paenian/Delta-Conveyor-Belt/kossel - 240mm triangle/ancillary STLs/HVplate.stl

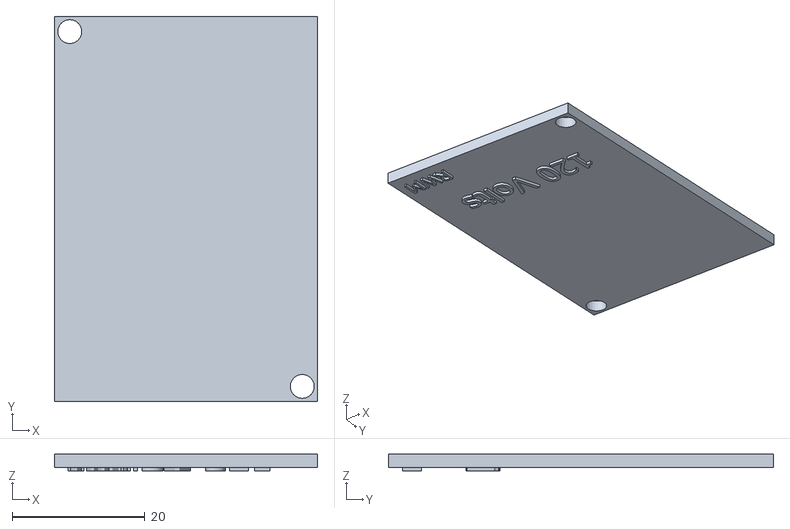
[picture p16: CAD file, 2020-08-09]
kossel - 240mm triangle/ancillary STLs/HVplate.stl
39.6 x 58.1 x 2.50
