paenian/Delta-Conveyor-Belt/kossel - 240mm triangle/motor_drive_gear.stl

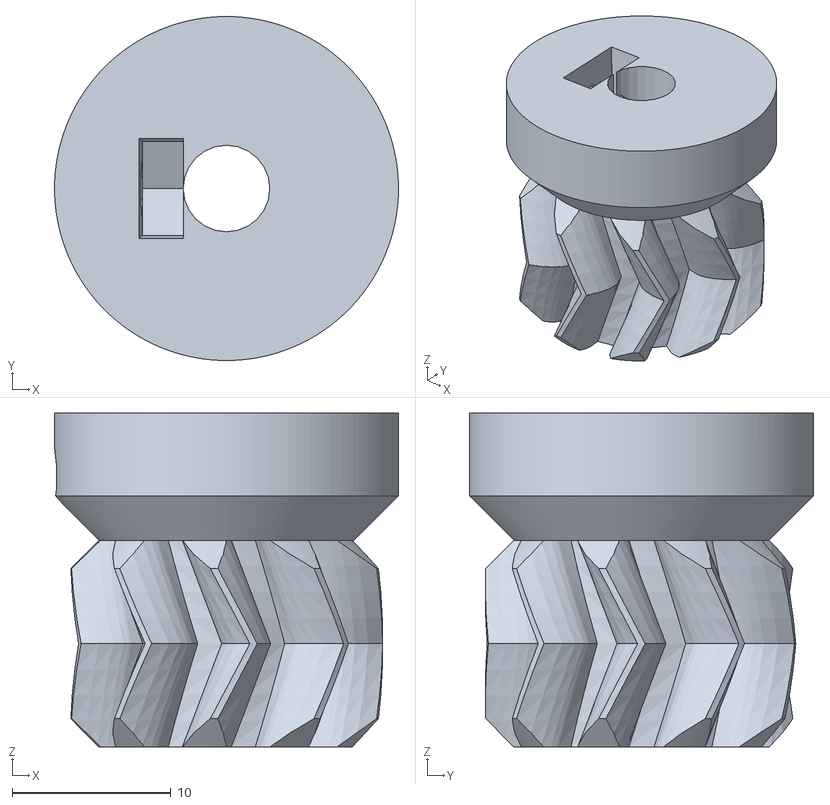
[picture p17: CAD file, 2020-04-07]
kossel - 240mm triangle/motor_drive_gear.stl
21.6 x 21.6 x 21.0
