paenian/Delta-Conveyor-Belt/kossel linear plus/triangles.dxf

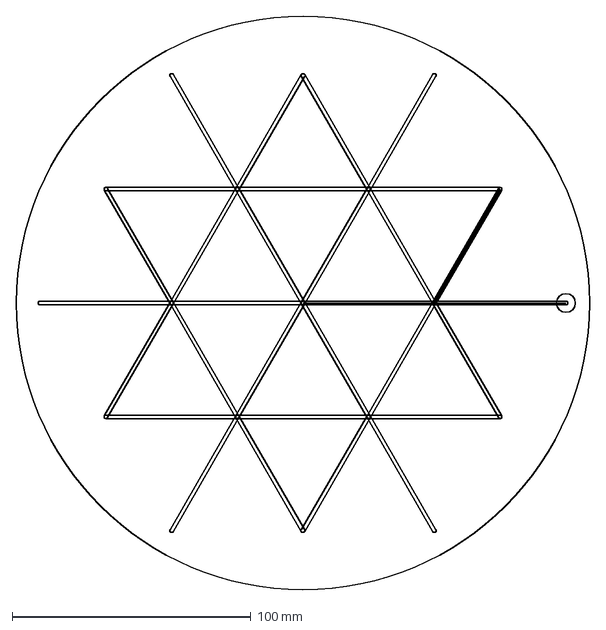
[picture p18: CAD file, 2020-09-24]
kossel linear plus/triangles.dxf
240.0 x 240.0 mm
