paenian/Delta-Conveyor-Belt/prusa mini/bed lasercutting/rounded_notch-425x155.dxf

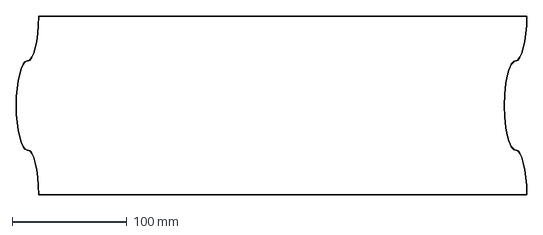
[picture p19: CAD file, 2021-02-12]
prusa mini/bed lasercutting/rounded_notch-425x155.dxf
444.4 x 155.0 mm
