paenian/Delta-Conveyor-Belt/prusa mini/ejector 2.0/rear motor clamp.stl

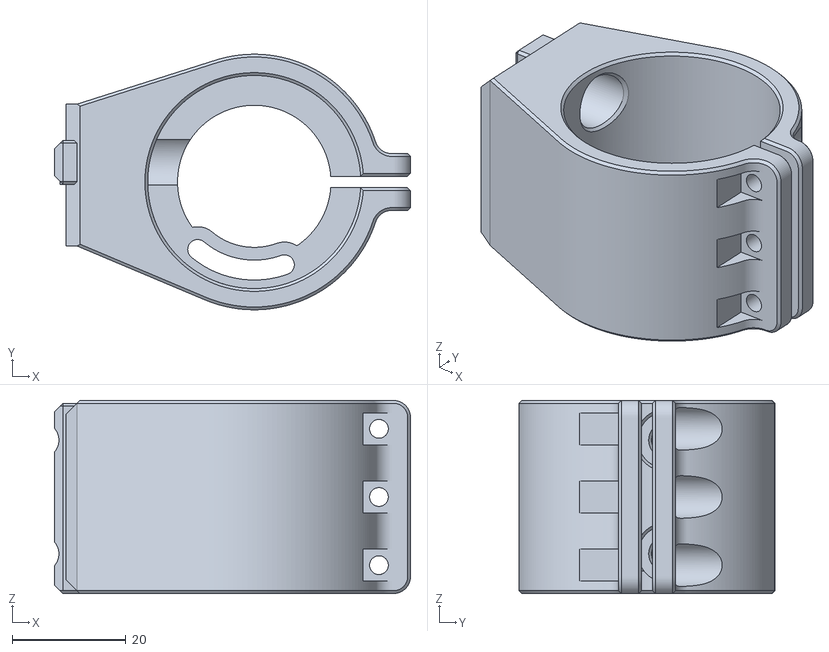
[picture p20: CAD file, 2021-02-12]
prusa mini/ejector 2.0/rear motor clamp.stl
62.7 x 45.0 x 34.0
