paenian/Delta-Conveyor-Belt/prusa mini/ejector 3.0/failed coupler iterations/rear motor plate.stl

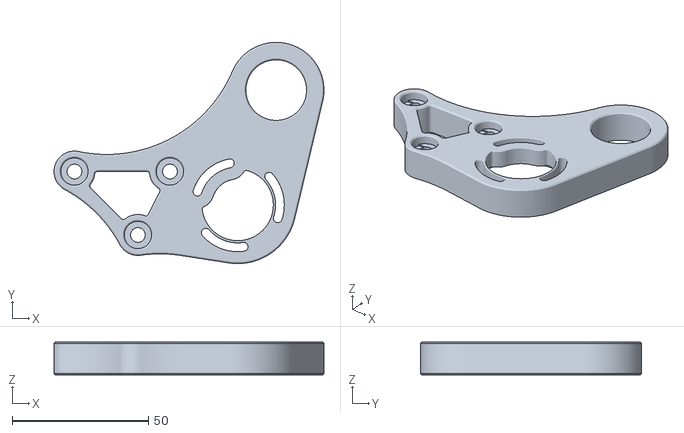
[picture p21: CAD file, 2021-04-25]
prusa mini/ejector 3.0/failed coupler iterations/rear motor plate.stl
98.9 x 81.1 x 12.0
