paenian/Delta-Conveyor-Belt/prusa mini/ejector 3.0/pi_3_case_bottom.stl

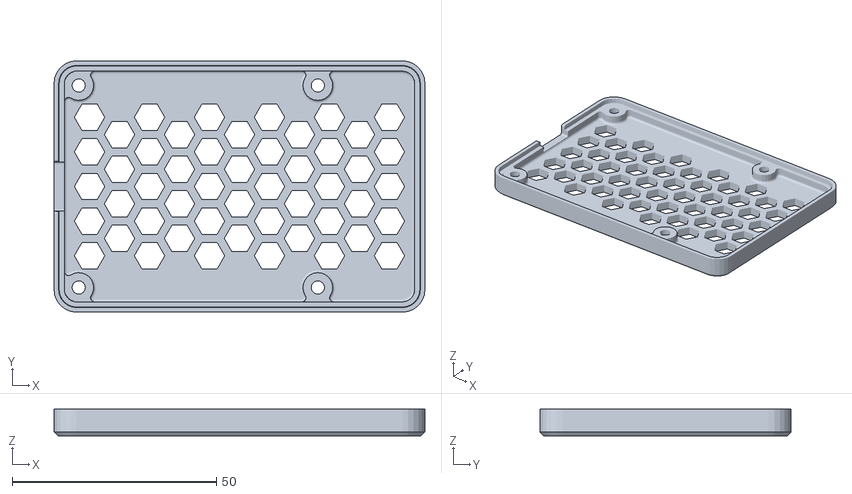
[picture p22: CAD file, 2021-04-25]
prusa mini/ejector 3.0/pi_3_case_bottom.stl
90.9 x 61.6 x 6.57
