paenian/Delta-Conveyor-Belt/prusa mini/experimental parts/motor_gear.stl

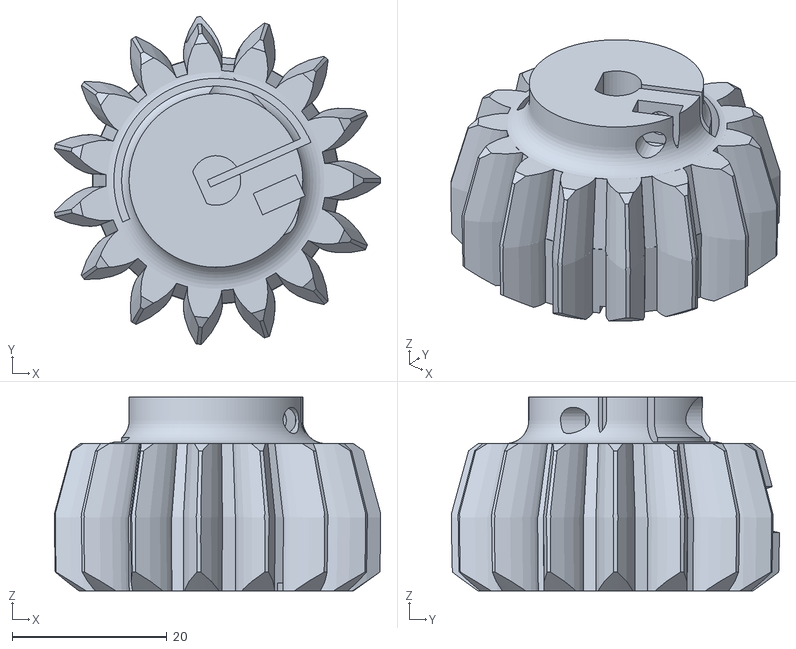
[picture p23: CAD file, 2021-02-12]
prusa mini/experimental parts/motor_gear.stl
42.1 x 42.3 x 25.0
