paenian/Delta-Conveyor-Belt/prusa mini/front spool holder.stl

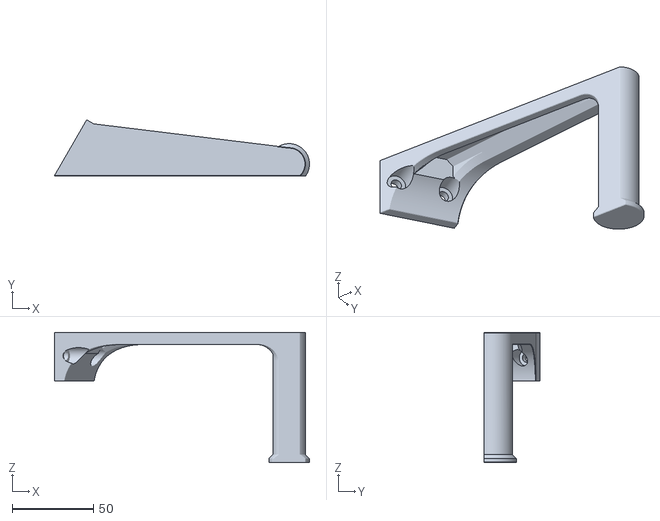
[picture p24: CAD file, 2020-11-18]
prusa mini/front spool holder.stl
156.6 x 34.6 x 80.0
