paenian/Delta-Conveyor-Belt/prusa mini/raspi/pi camera mount.stl

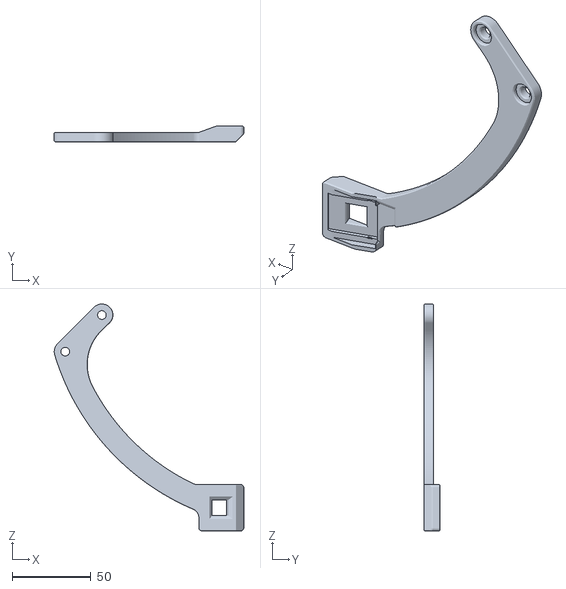
[picture p25: CAD file, 2020-11-18]
prusa mini/raspi/pi camera mount.stl
120.2 x 10.0 x 144.0
