paenian/Delta-Conveyor-Belt/tft35right.stl

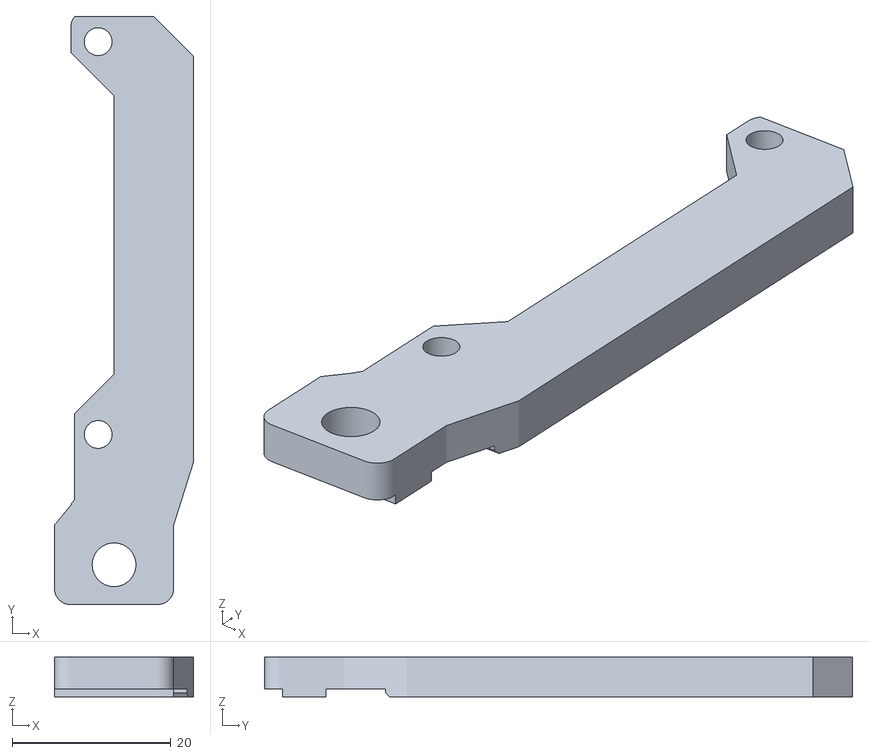
[picture p26: CAD file, 2020-08-09]
tft35right.stl
17.5 x 74.0 x 5.00
