paenian/Delta-Conveyor-Belt/kossel - 240mm triangle/ancillary STLs/pwr_shield4.stl

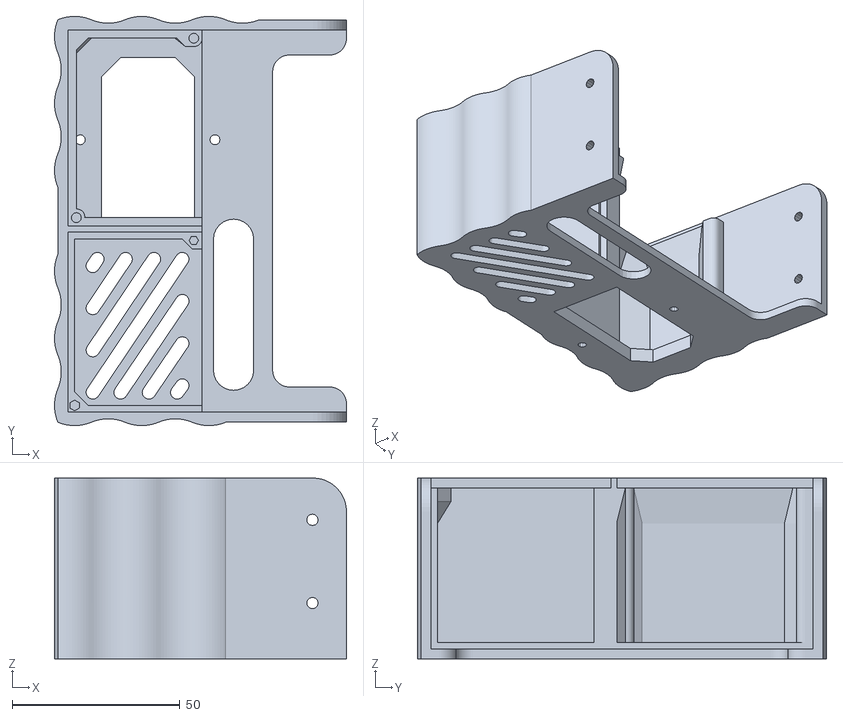
[picture p27: CAD file, 2020-08-09]
kossel - 240mm triangle/ancillary STLs/pwr_shield4.stl
87.0 x 121.9 x 53.9
