paenian/Delta-Conveyor-Belt/kossel - 240mm triangle/fan mount.stl

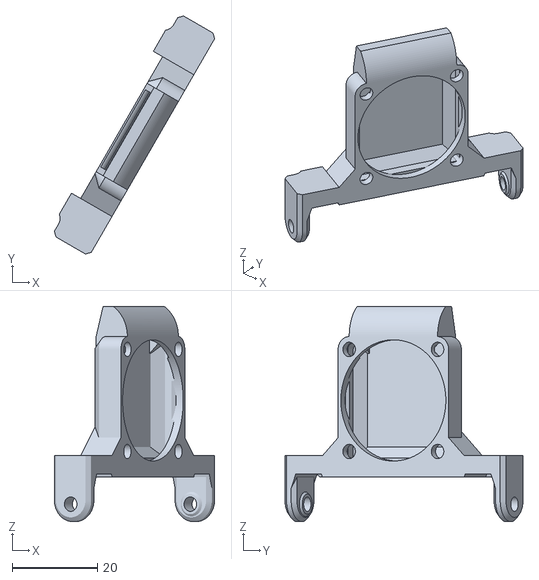
[picture p28: CAD file, 2020-04-07]
kossel - 240mm triangle/fan mount.stl
37.7 x 56.0 x 50.6
