paenian/Delta-Conveyor-Belt/kossel linear plus/o-ring groove.dxf

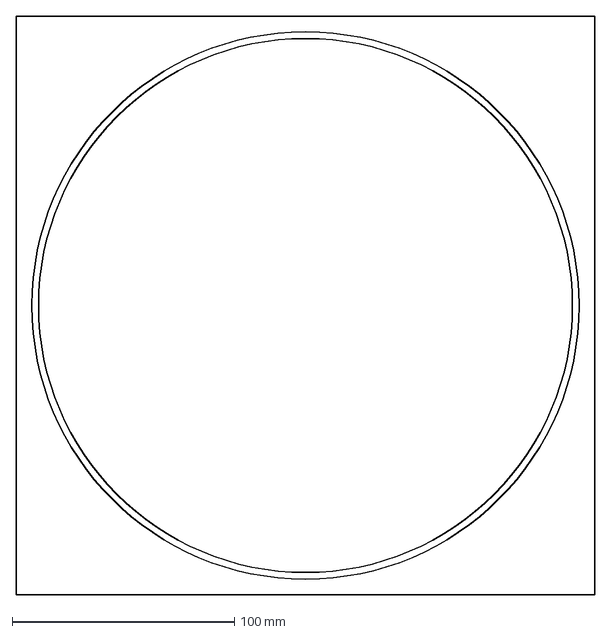
[picture p29: CAD file, 2020-09-24]
kossel linear plus/o-ring groove.dxf
260.0 x 260.0 mm
