paenian/Delta-Conveyor-Belt/prusa mini/bed lasercutting/chevron-425x155.dxf

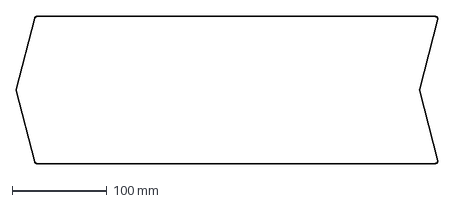
[picture p30: CAD file, 2021-02-12]
prusa mini/bed lasercutting/chevron-425x155.dxf
444.3 x 155.0 mm
