paenian/Delta-Conveyor-Belt/prusa mini/ejector 2.0/tensioner body.stl

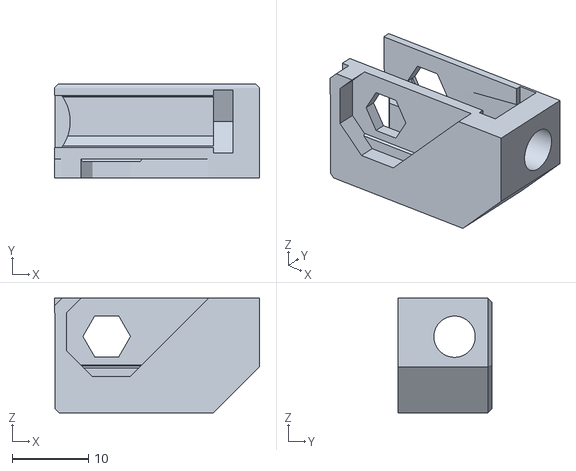
[picture p31: CAD file, 2021-02-12]
prusa mini/ejector 2.0/tensioner body.stl
26.8 x 12.3 x 15.0
