paenian/Delta-Conveyor-Belt/prusa mini/ejector 3.0/failed coupler iterations/Body37.stl

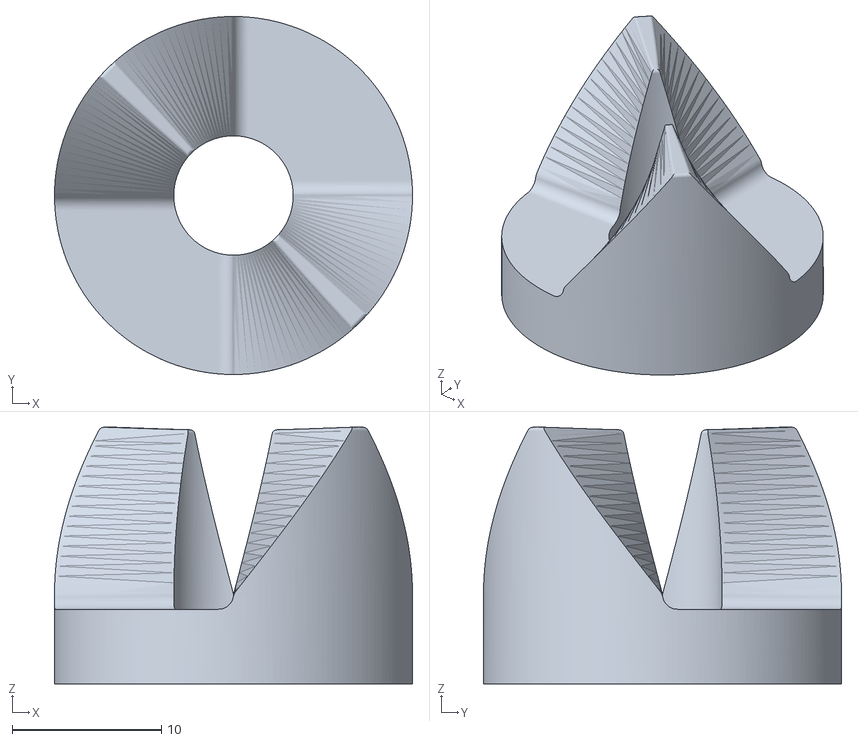
[picture p32: CAD file, 2021-02-26]
prusa mini/ejector 3.0/failed coupler iterations/Body37.stl
24.0 x 24.0 x 17.2
