paenian/Delta-Conveyor-Belt/prusa mini/ejector 3.0/pi_3_case_top.stl

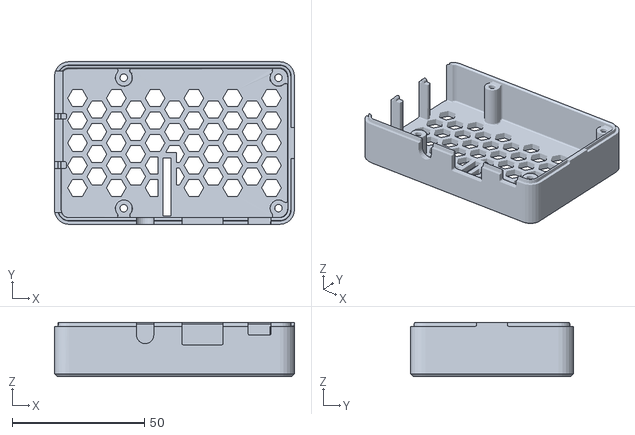
[picture p33: CAD file, 2021-04-25]
prusa mini/ejector 3.0/pi_3_case_top.stl
90.9 x 61.6 x 20.5
