paenian/Delta-Conveyor-Belt/prusa mini/experimental parts/belt_gear.stl

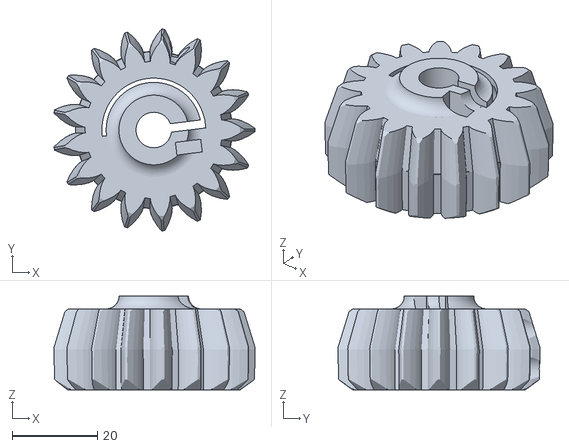
[picture p34: CAD file, 2021-02-12]
prusa mini/experimental parts/belt_gear.stl
47.2 x 47.4 x 22.0
