paenian/Delta-Conveyor-Belt/prusa mini/motor_gear.stl

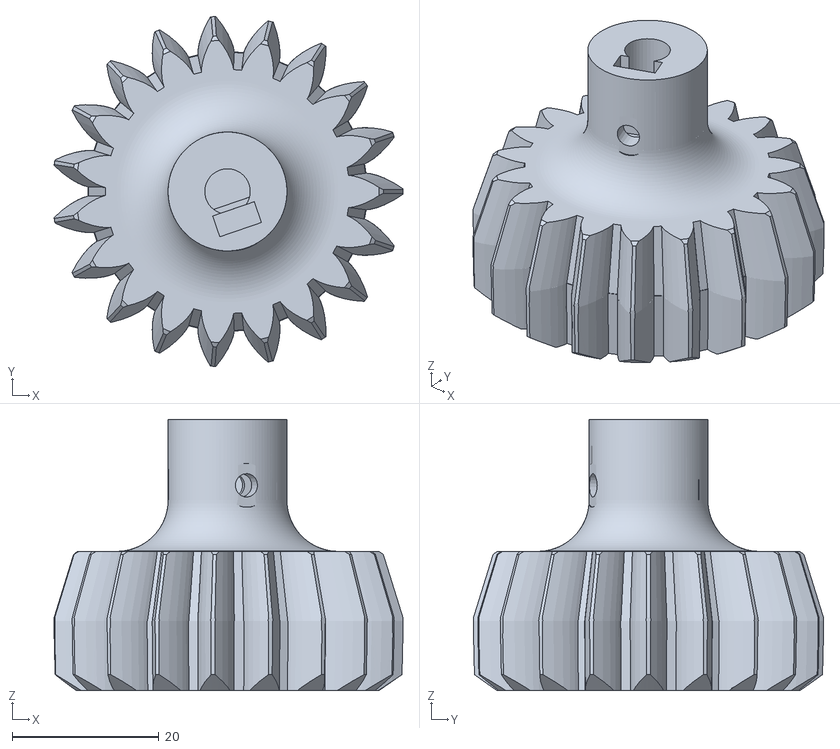
[picture p35: CAD file, 2020-11-18]
prusa mini/motor_gear.stl
47.6 x 47.7 x 37.0
