paenian/Delta-Conveyor-Belt/prusa mini/raspi/raspi_case_top.stl

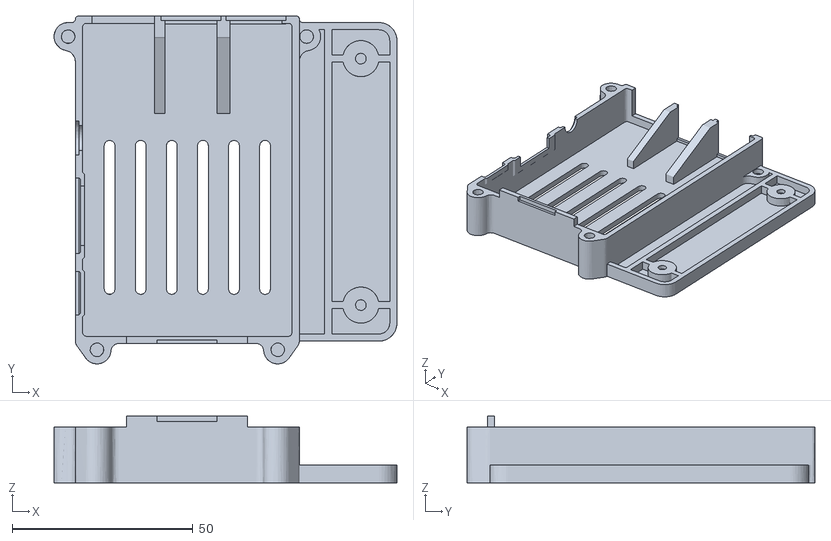
[picture p36: CAD file, 2020-08-16]
prusa mini/raspi/raspi_case_top.stl
94.9 x 96.2 x 18.5
