paenian/Delta-Conveyor-Belt/tft35left.stl

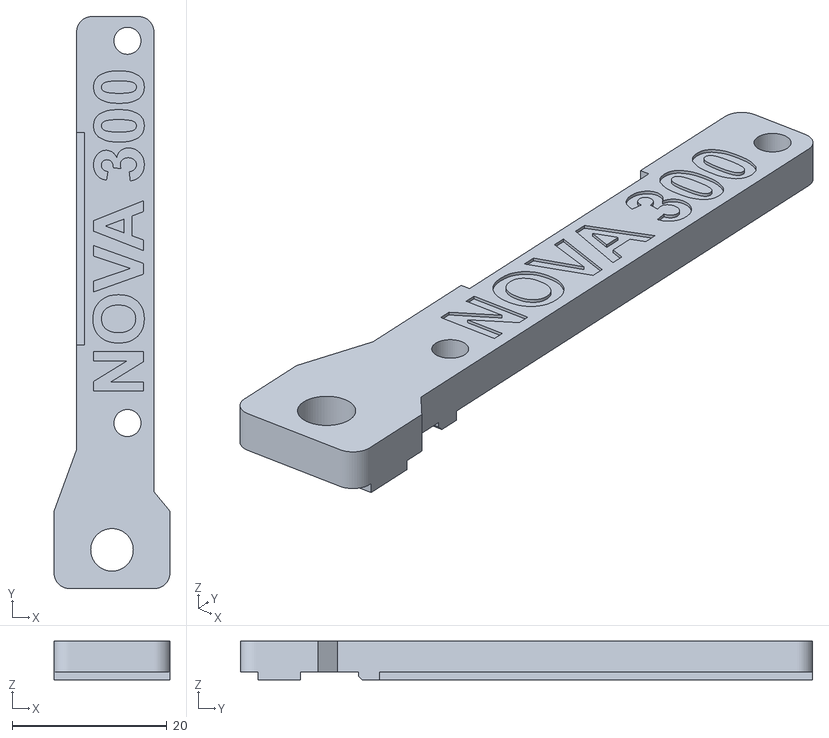
[picture p37: CAD file, 2020-08-09]
tft35left.stl
15.0 x 74.0 x 5.00
