paenian/Delta-Conveyor-Belt/kossel - 240mm triangle/ancillary STLs/LVplate.stl

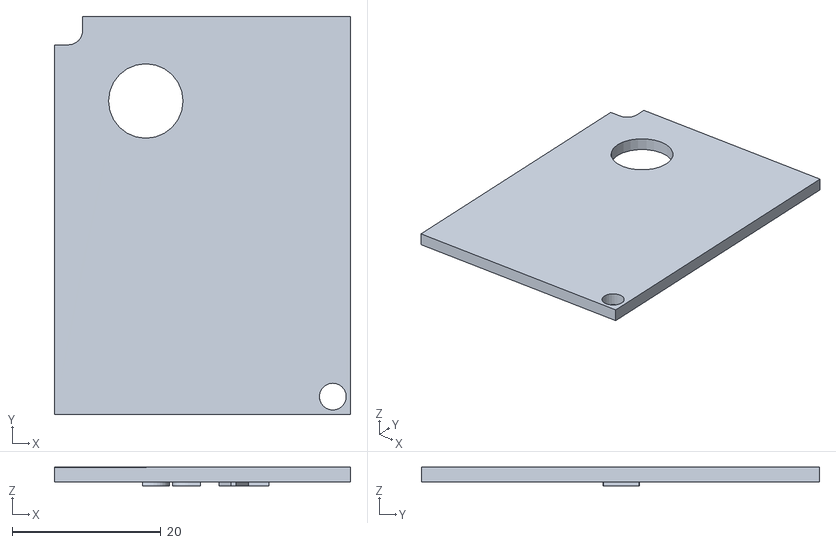
[picture p38: CAD file, 2020-08-09]
kossel - 240mm triangle/ancillary STLs/LVplate.stl
39.8 x 53.5 x 2.51
