paenian/Delta-Conveyor-Belt/kossel linear plus/vacuum hole.dxf

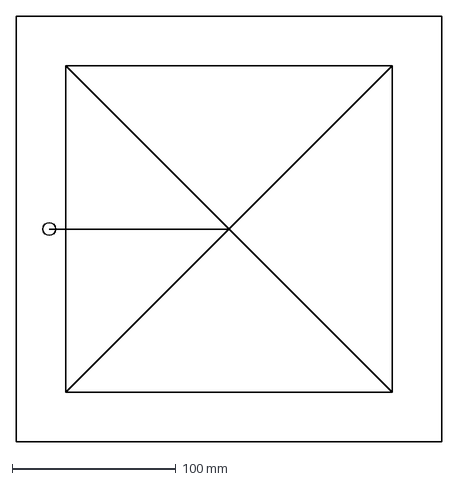
[picture p39: CAD file, 2020-09-24]
kossel linear plus/vacuum hole.dxf
260.0 x 260.0 mm
