paenian/Delta-Conveyor-Belt/prusa mini/belt_425mm.dxf

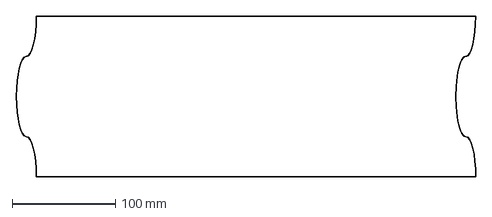
[picture p40: CAD file, 2020-11-02]
prusa mini/belt_425mm.dxf
444.4 x 155.0 mm
