paenian/Delta-Conveyor-Belt/prusa mini/ejector 2.0/lifted belt shaft mount - fixed bushing.stl

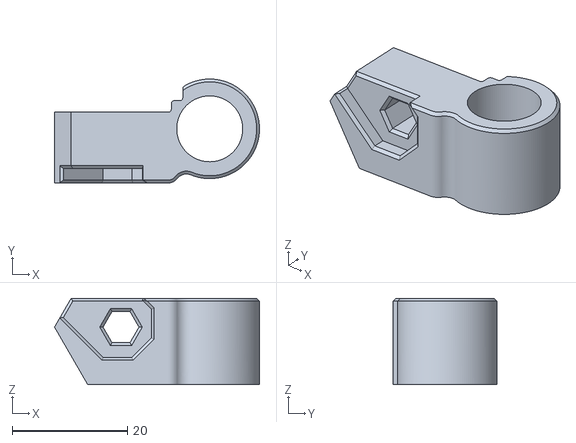
[picture p41: CAD file, 2021-02-12]
prusa mini/ejector 2.0/lifted belt shaft mount - fixed bushing.stl
35.6 x 18.0 x 15.0
