paenian/Delta-Conveyor-Belt/prusa mini/ejector 3.0/failed coupler iterations/split_spider.stl

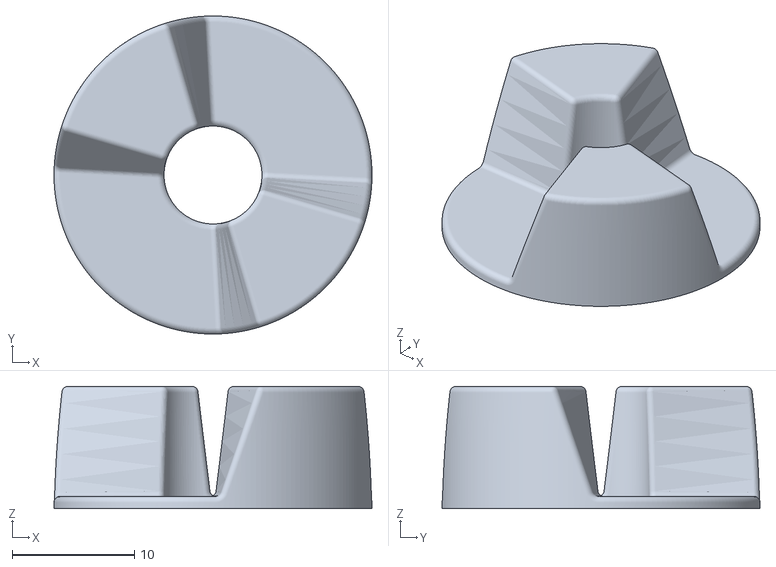
[picture p42: CAD file, 2021-02-26]
prusa mini/ejector 3.0/failed coupler iterations/split_spider.stl
26.0 x 26.0 x 10.0
