paenian/Delta-Conveyor-Belt/prusa mini/ejector 3.0/rear motor plate.stl

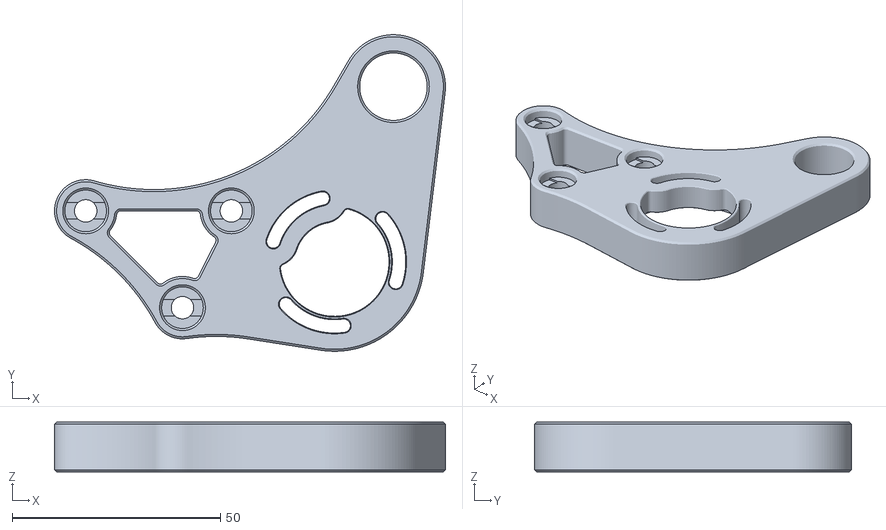
[picture p43: CAD file, 2021-03-26]
prusa mini/ejector 3.0/rear motor plate.stl
93.9 x 76.1 x 12.0
