paenian/Delta-Conveyor-Belt/prusa mini/experimental parts/foot.stl

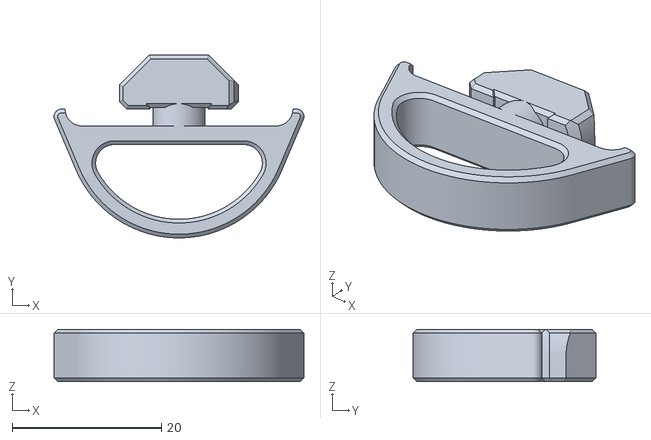
[picture p44: CAD file, 2021-02-12]
prusa mini/experimental parts/foot.stl
33.5 x 24.5 x 7.00
