paenian/Delta-Conveyor-Belt/prusa mini/raspi/raspi_case_bottom.stl

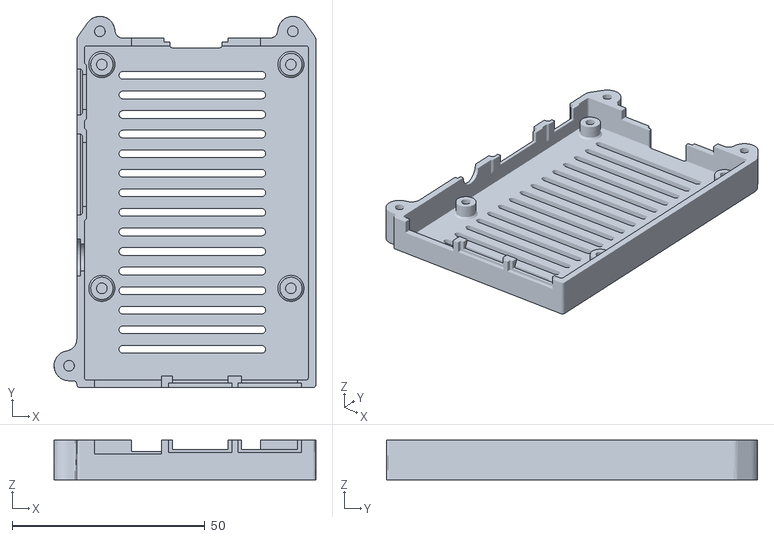
[picture p45: CAD file, 2020-08-16]
prusa mini/raspi/raspi_case_bottom.stl
67.9 x 96.2 x 10.3
