paenian/Delta-Conveyor-Belt/tft24left.stl

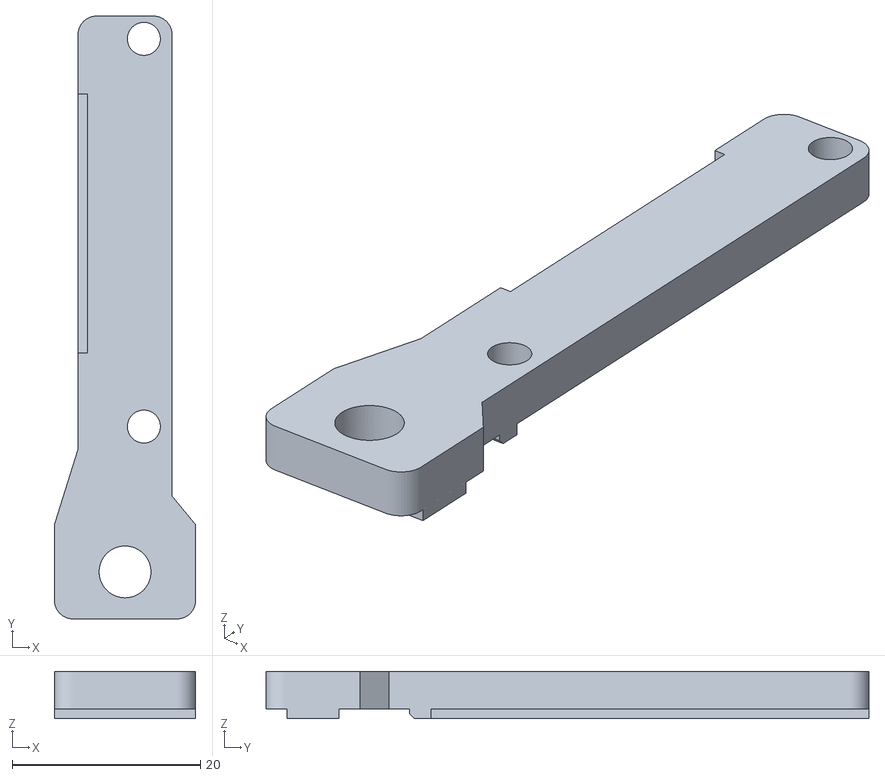
[picture p46: CAD file, 2020-08-09]
tft24left.stl
15.0 x 64.0 x 5.00
