paenian/Delta-Conveyor-Belt/kossel - 240mm triangle/ancillary STLs/Raspberry_Pi_3_Case_-_Bottom.stl

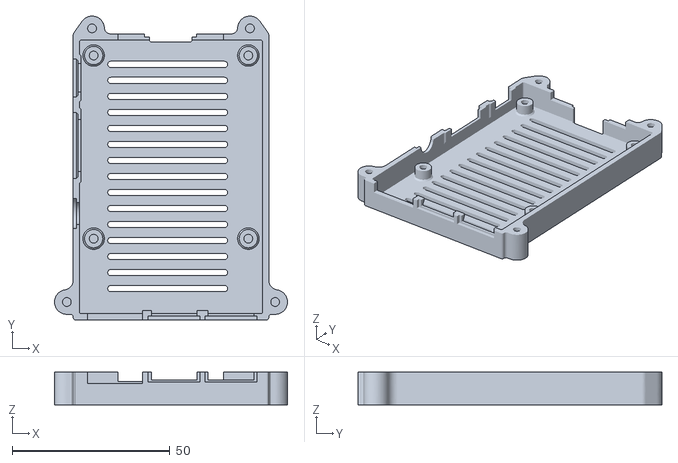
[picture p47: CAD file, 2020-08-09]
kossel - 240mm triangle/ancillary STLs/Raspberry_Pi_3_Case_-_Bottom.stl
73.8 x 96.2 x 10.3
