paenian/Delta-Conveyor-Belt/kossel - 240mm triangle/tensioner arm(Mirror).stl

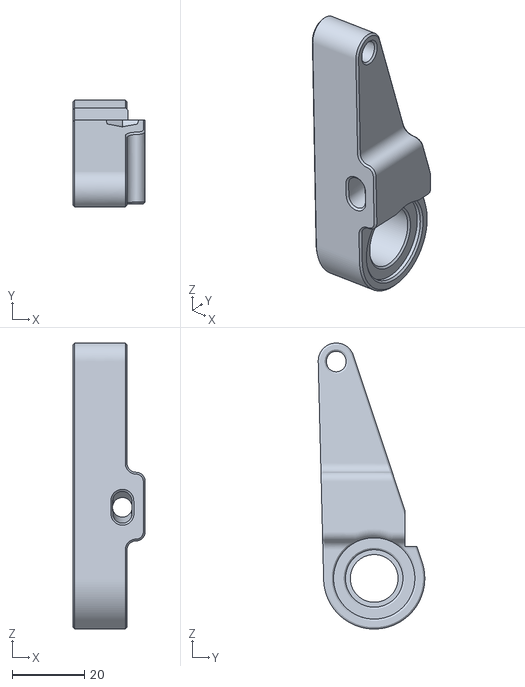
[picture p48: CAD file, 2020-04-07]
kossel - 240mm triangle/tensioner arm(Mirror).stl
20.0 x 29.5 x 79.1
