paenian/Delta-Conveyor-Belt/prusa mini/ejector 2.0/rear motor plate.stl

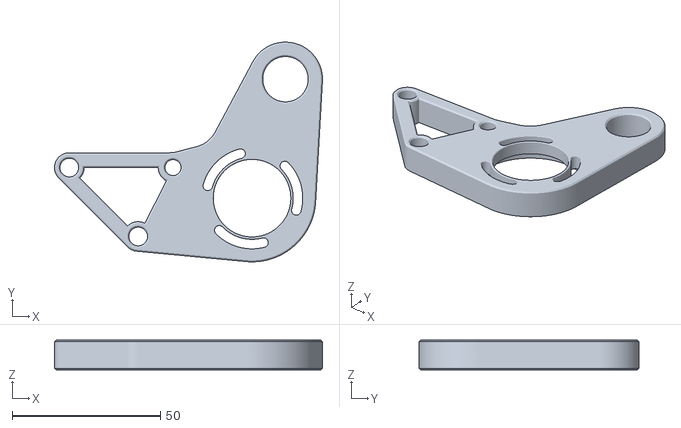
[picture p49: CAD file, 2021-02-12]
prusa mini/ejector 2.0/rear motor plate.stl
90.4 x 74.2 x 10.0
