paenian/Delta-Conveyor-Belt/prusa mini/ejector 3.0/failed coupler iterations/coupler_adapter.stl

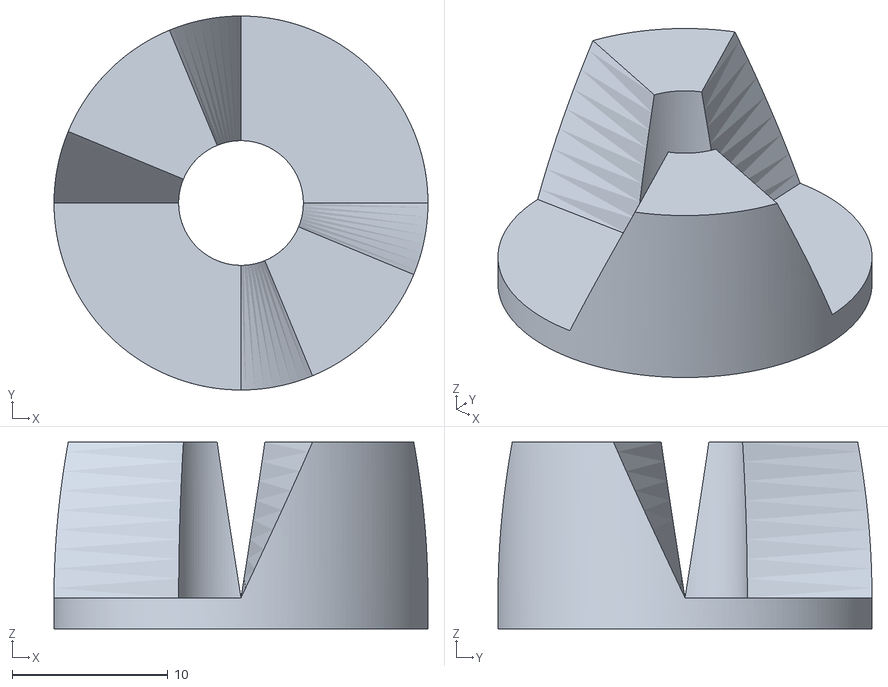
[picture p50: CAD file, 2021-02-26]
prusa mini/ejector 3.0/failed coupler iterations/coupler_adapter.stl
24.0 x 24.0 x 12.0
