paenian/Delta-Conveyor-Belt/prusa mini/raspi/3030-dropin-tee-m3.stl

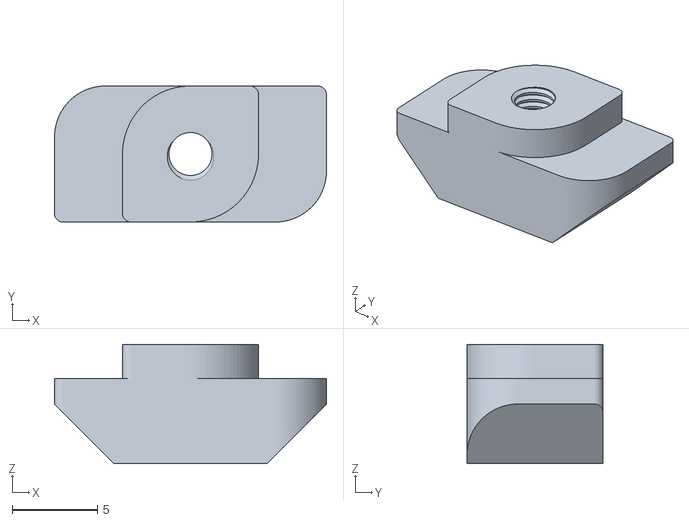
[picture p51: CAD file, 2020-08-09]
prusa mini/raspi/3030-dropin-tee-m3.stl
16.0 x 8.00 x 7.00
