paenian/Delta-Conveyor-Belt/prusa mini/small_base_light.stl

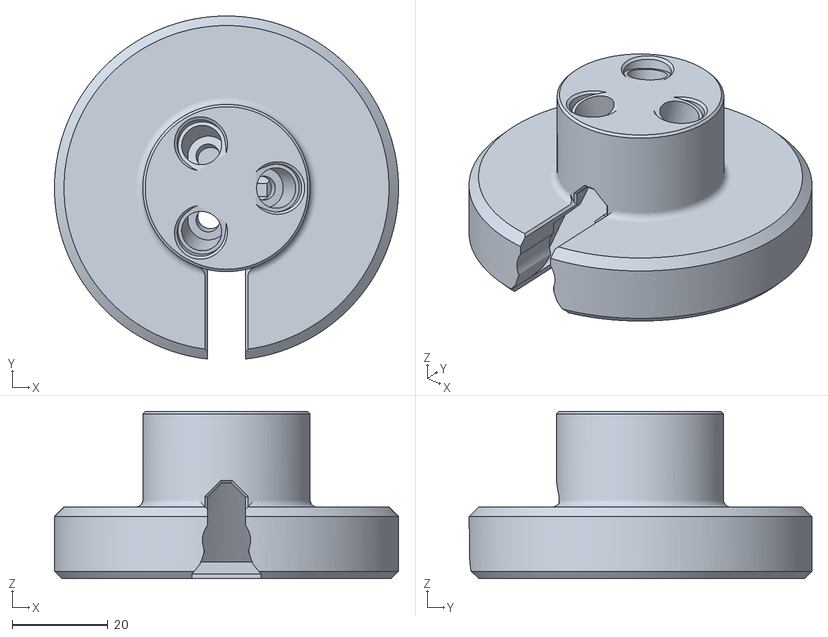
[picture p52: CAD file, 2020-10-20]
prusa mini/small_base_light.stl
72.0 x 71.8 x 35.0
