paenian/Delta-Conveyor-Belt/tft24right.stl

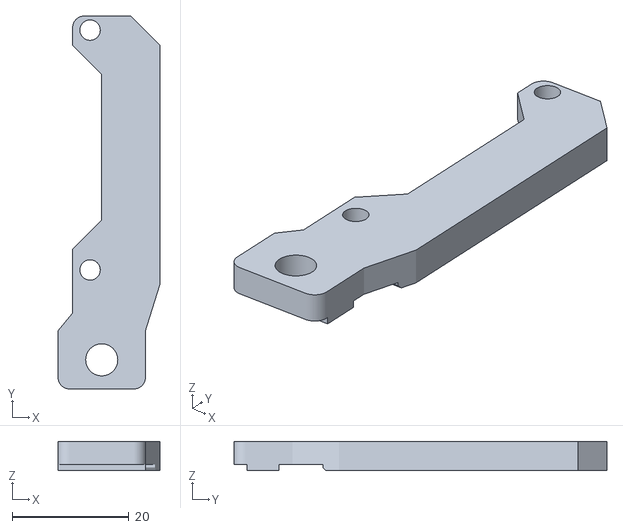
[picture p53: CAD file, 2020-08-09]
tft24right.stl
17.5 x 64.0 x 5.00
