paenian/Delta-Conveyor-Belt/kossel - 240mm triangle/ancillary STLs/psu_bracket.stl

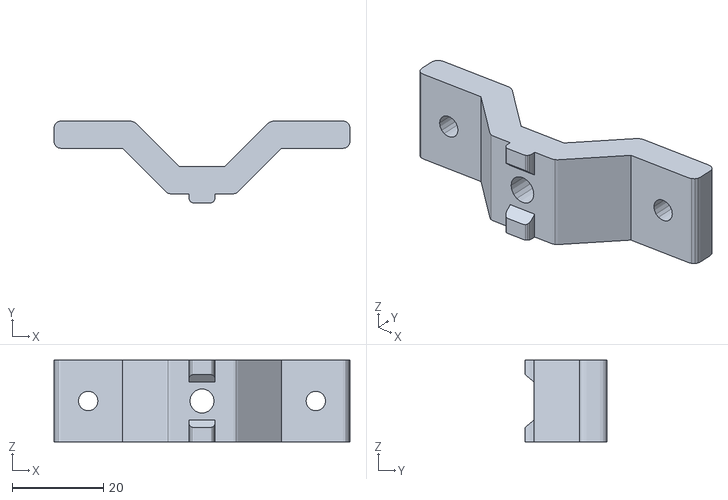
[picture p54: CAD file, 2020-04-07]
kossel - 240mm triangle/ancillary STLs/psu_bracket.stl
65.0 x 18.0 x 18.0
