paenian/Delta-Conveyor-Belt/prusa mini/bed center support.stl

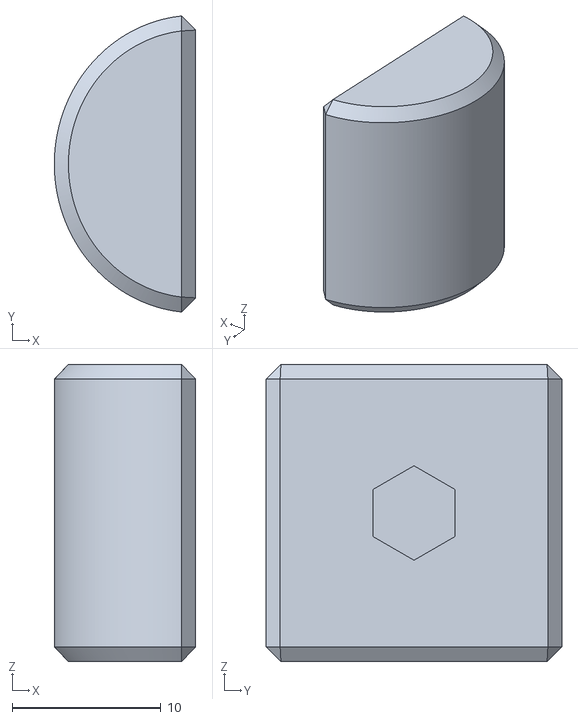
[picture p55: CAD file, 2020-10-20]
prusa mini/bed center support.stl
9.50 x 19.9 x 20.0
