paenian/Delta-Conveyor-Belt/prusa mini/ejector 2.0/belt_gear.stl

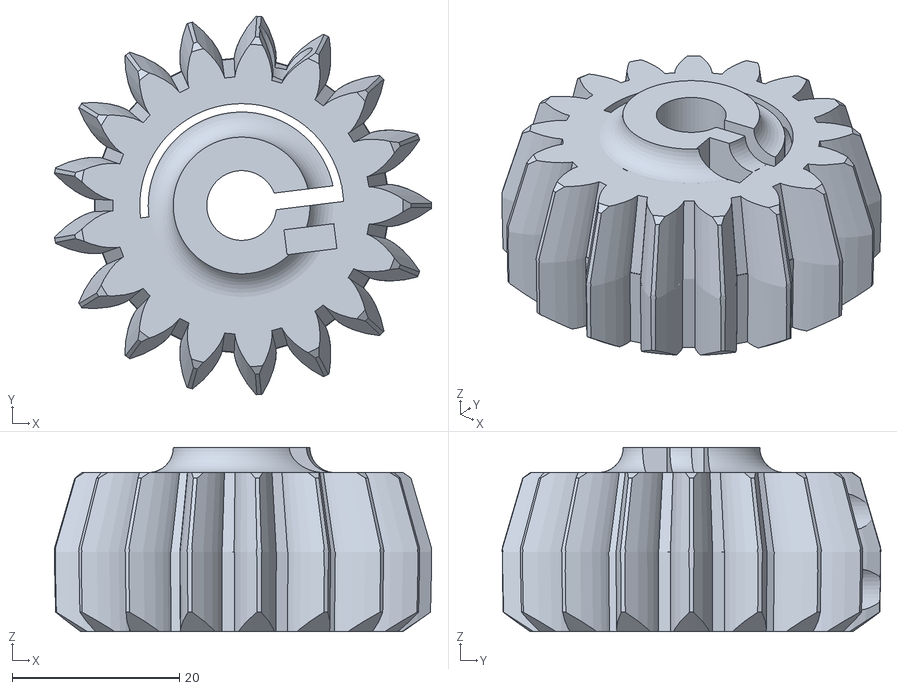
[picture p56: CAD file, 2020-12-29]
prusa mini/ejector 2.0/belt_gear.stl
45.1 x 45.3 x 22.0
