paenian/Delta-Conveyor-Belt/prusa mini/ejector 3.0/failed coupler iterations/5mm shaft side.stl

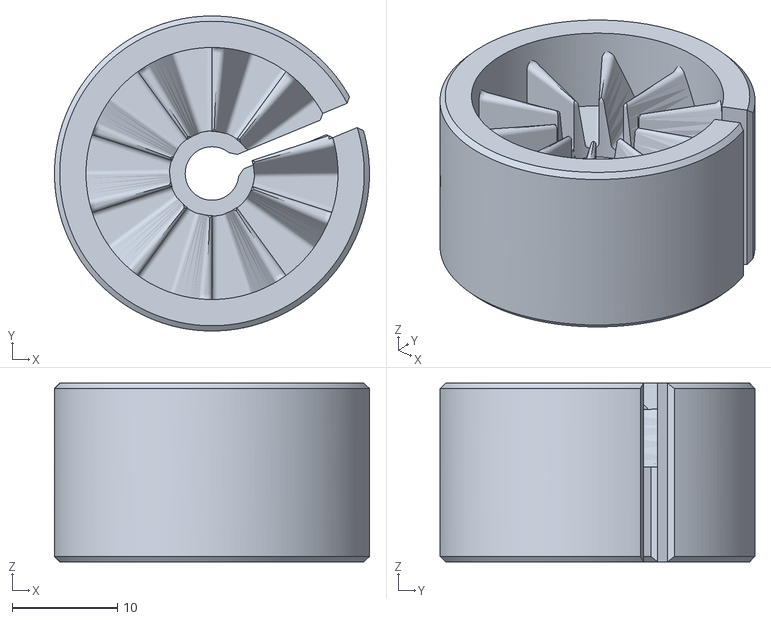
[picture p57: CAD file, 2021-02-19]
prusa mini/ejector 3.0/failed coupler iterations/5mm shaft side.stl
30.0 x 30.0 x 17.0
