paenian/Delta-Conveyor-Belt/prusa mini/ejector 3.0/motor plate standoff - with pi.stl

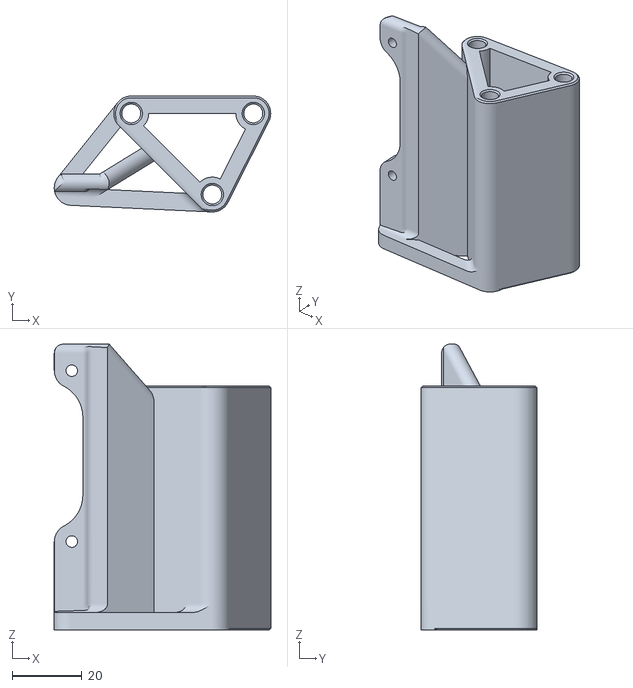
[picture p58: CAD file, 2021-02-19]
prusa mini/ejector 3.0/motor plate standoff - with pi.stl
62.1 x 33.2 x 82.0
