paenian/Delta-Conveyor-Belt/tensioner mount.stl

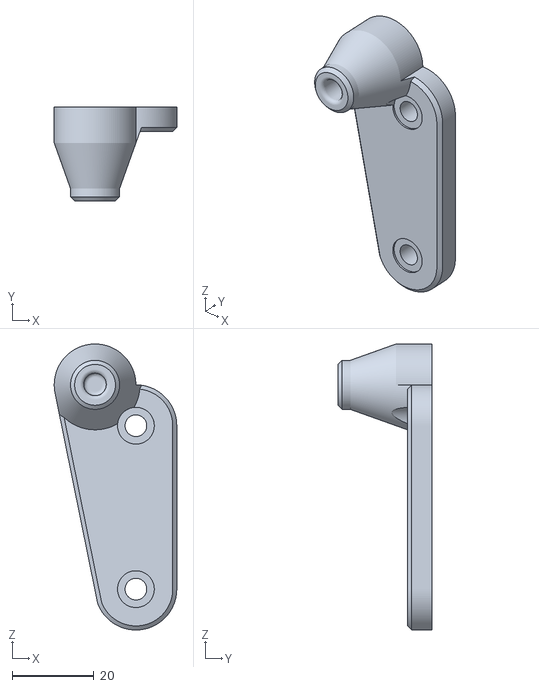
[picture p59: CAD file, 2020-04-07]
tensioner mount.stl
30.0 x 23.0 x 70.0
