paenian/Delta-Conveyor-Belt/kossel - 240mm triangle/bltouch mount.stl

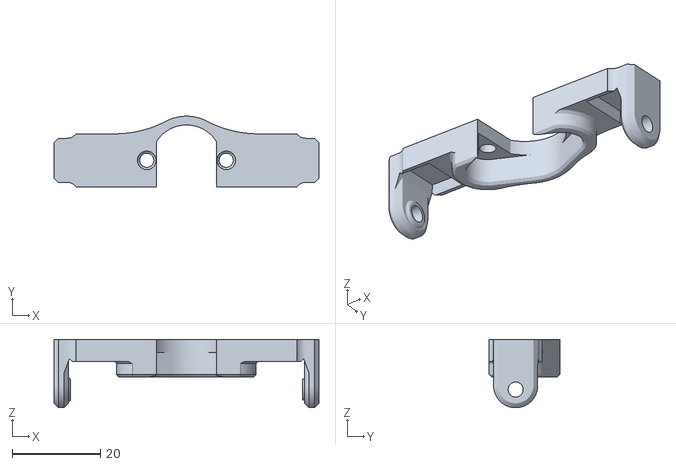
[picture p60: CAD file, 2020-04-07]
kossel - 240mm triangle/bltouch mount.stl
60.0 x 16.0 x 15.5
