paenian/Delta-Conveyor-Belt/prusa mini/ejector 2.0/lifted tensioner rod holder.stl

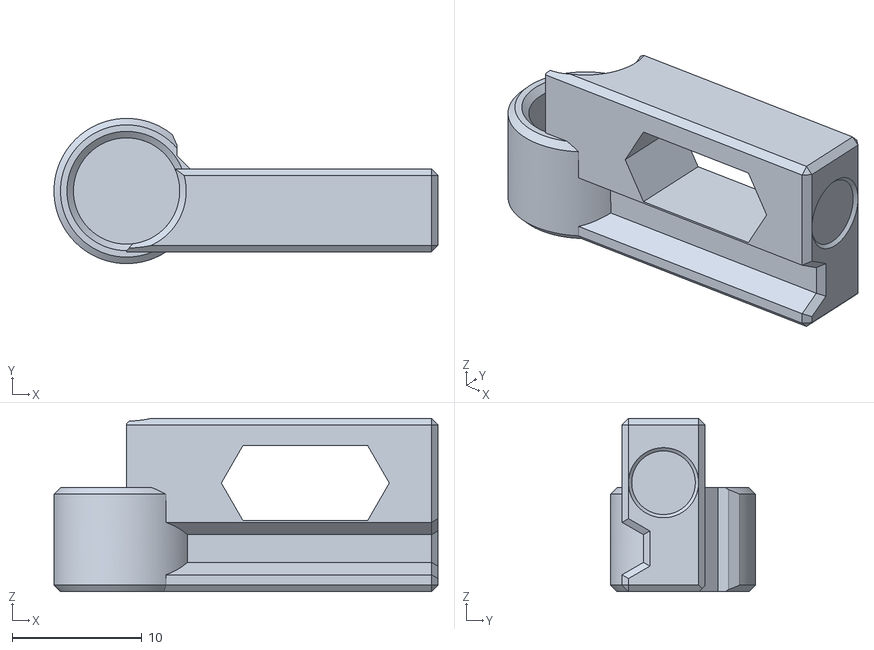
[picture p61: CAD file, 2020-11-18]
prusa mini/ejector 2.0/lifted tensioner rod holder.stl
29.6 x 11.2 x 13.3
