paenian/Delta-Conveyor-Belt/prusa mini/ejector 3.0/failed coupler iterations/8mm shaft side.stl

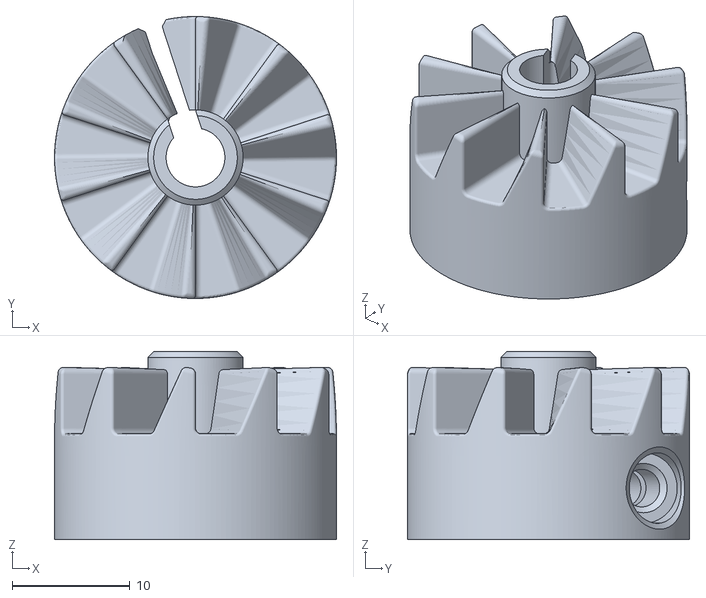
[picture p62: CAD file, 2021-02-19]
prusa mini/ejector 3.0/failed coupler iterations/8mm shaft side.stl
24.0 x 24.0 x 16.0
