paenian/Delta-Conveyor-Belt/prusa mini/ejector 3.0/pi_support.stl

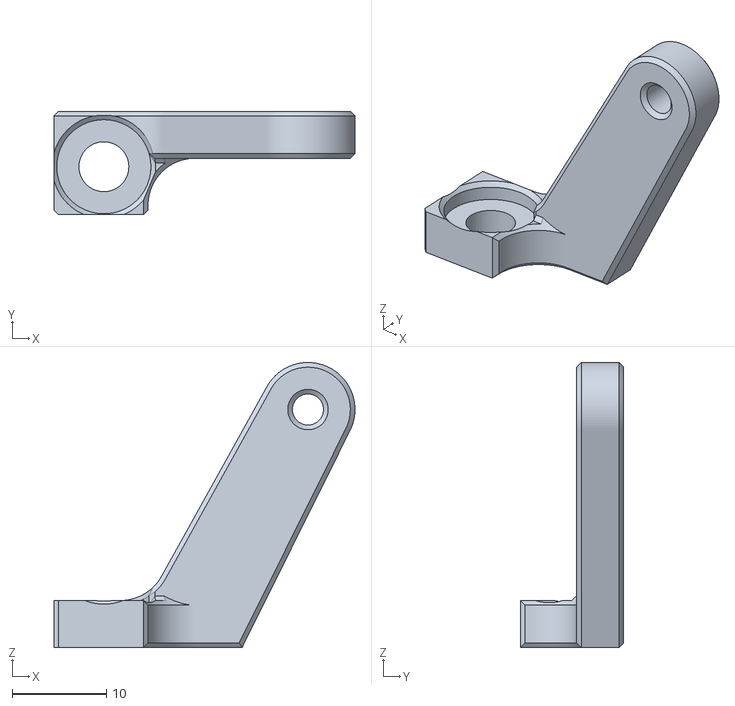
[picture p63: CAD file, 2021-02-19]
prusa mini/ejector 3.0/pi_support.stl
32.0 x 11.0 x 30.3
