paenian/Delta-Conveyor-Belt/tensioner rod.stl

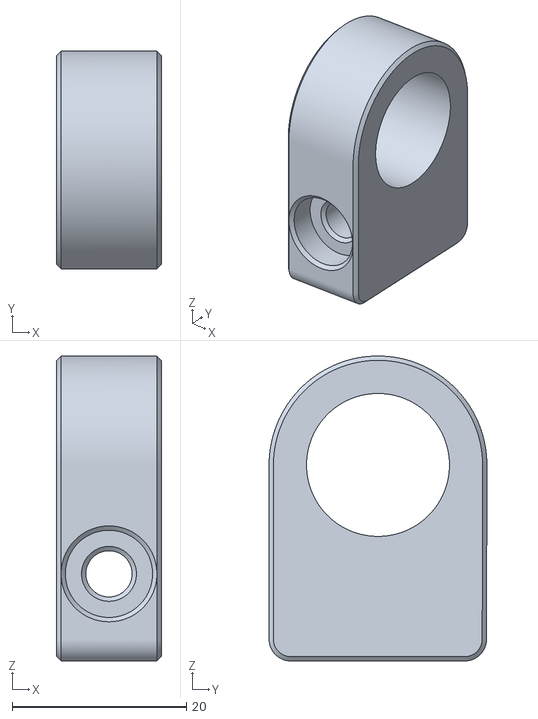
[picture p64: CAD file, 2020-04-07]
tensioner rod.stl
12.0 x 25.0 x 35.0
