paenian/Delta-Conveyor-Belt/bertha top bed.dxf

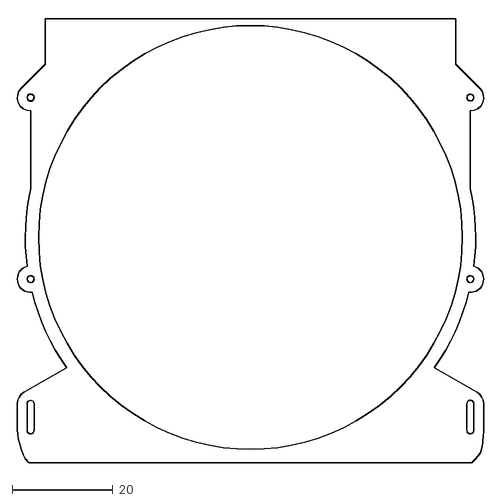
[picture p65: CAD file, 2020-03-01]
bertha top bed.dxf
93.0 x 88.7
