paenian/Delta-Conveyor-Belt/kossel - 240mm triangle/electronics top.stl

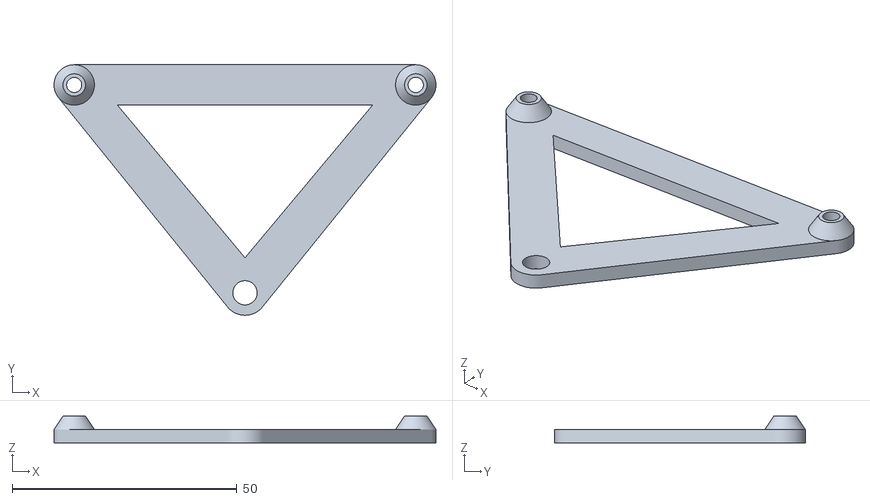
[picture p66: CAD file, 2020-04-07]
kossel - 240mm triangle/electronics top.stl
85.0 x 55.8 x 6.00
