paenian/Delta-Conveyor-Belt/prusa mini/ejector 3.0/failed coupler iterations/coupler spider.stl

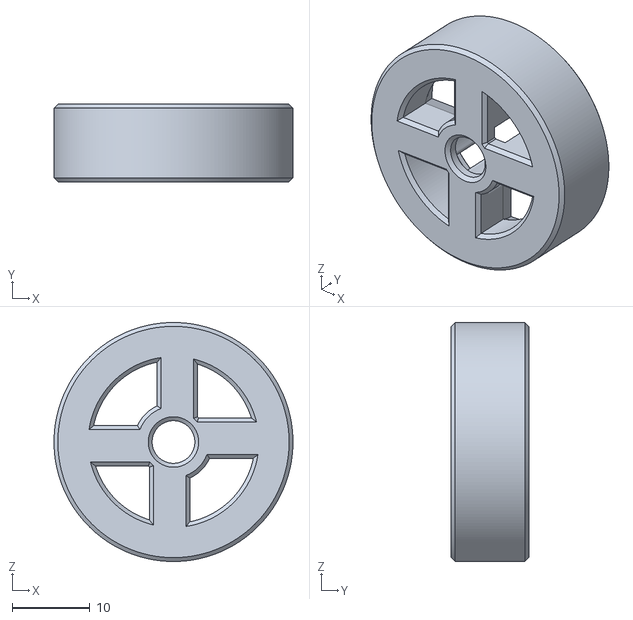
[picture p67: CAD file, 2021-02-19]
prusa mini/ejector 3.0/failed coupler iterations/coupler spider.stl
30.8 x 10.0 x 30.8
