paenian/Delta-Conveyor-Belt/prusa mini/ejector 3.0/Pi_4_Case_bottom v3.stl

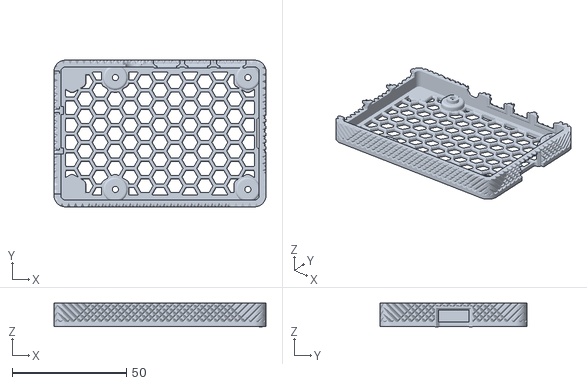
[picture p68: CAD file, 2021-02-19]
prusa mini/ejector 3.0/Pi_4_Case_bottom v3.stl
92.8 x 64.2 x 10.3
