paenian/Delta-Conveyor-Belt/prusa mini/lm8uu clamp.stl

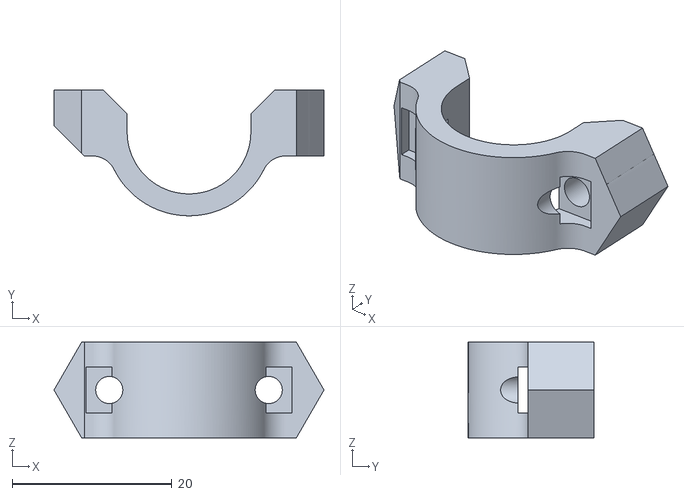
[picture p69: CAD file, 2020-10-14]
prusa mini/lm8uu clamp.stl
33.9 x 15.8 x 12.0
