paenian/Delta-Conveyor-Belt/extra bumper.stl

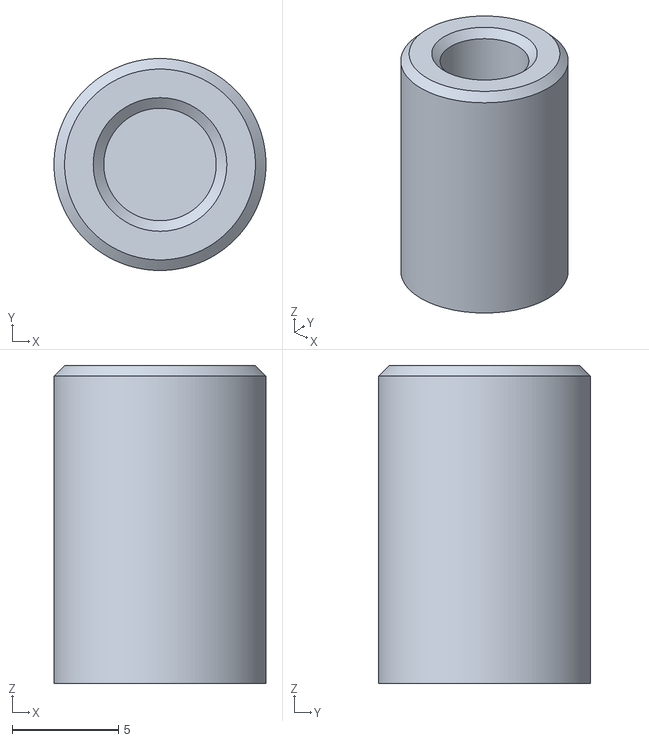
[picture p70: CAD file, 2020-03-01]
extra bumper.stl
10.00 x 10.00 x 15.0
