paenian/Delta-Conveyor-Belt/prusa mini/belt_gear.stl

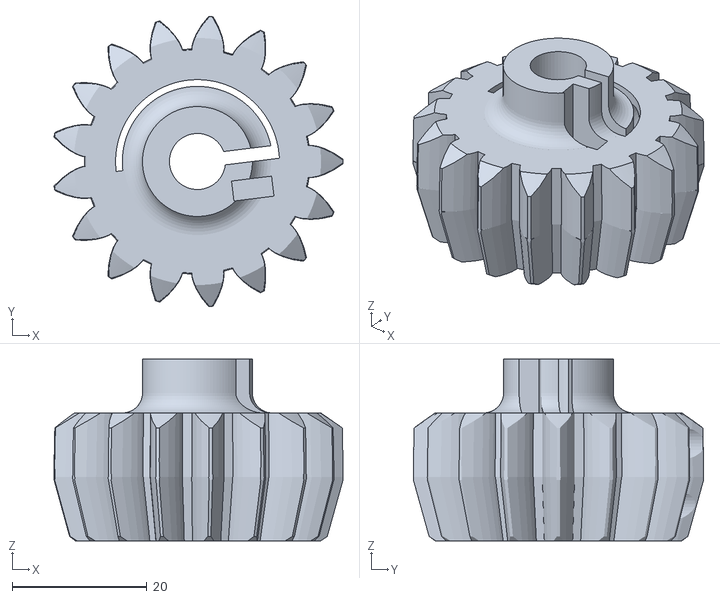
[picture p71: CAD file, 2020-10-14]
prusa mini/belt_gear.stl
43.0 x 43.1 x 27.0
