paenian/Delta-Conveyor-Belt/bump carriage.stl

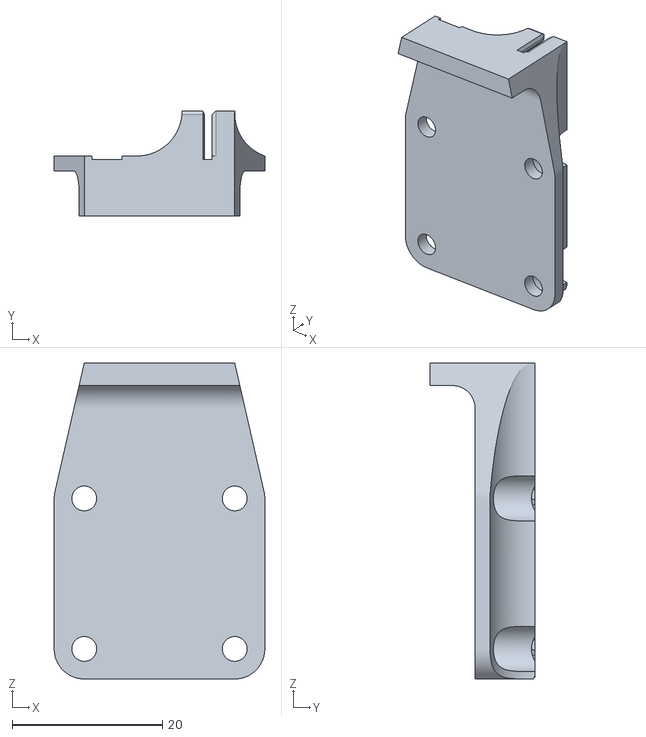
[picture p73: CAD file, 2020-03-01]
bump carriage.stl
28.0 x 14.0 x 42.0
