paenian/Delta-Conveyor-Belt/kossel - 240mm triangle/electronics side.stl

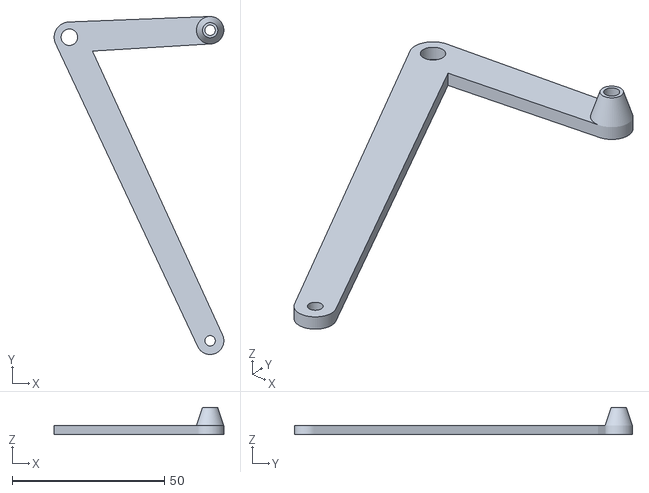
[picture p74: CAD file, 2020-04-07]
kossel - 240mm triangle/electronics side.stl
55.7 x 110.8 x 9.00
