paenian/Delta-Conveyor-Belt/prusa mini/ejector 3.0/motor plate standoff.stl

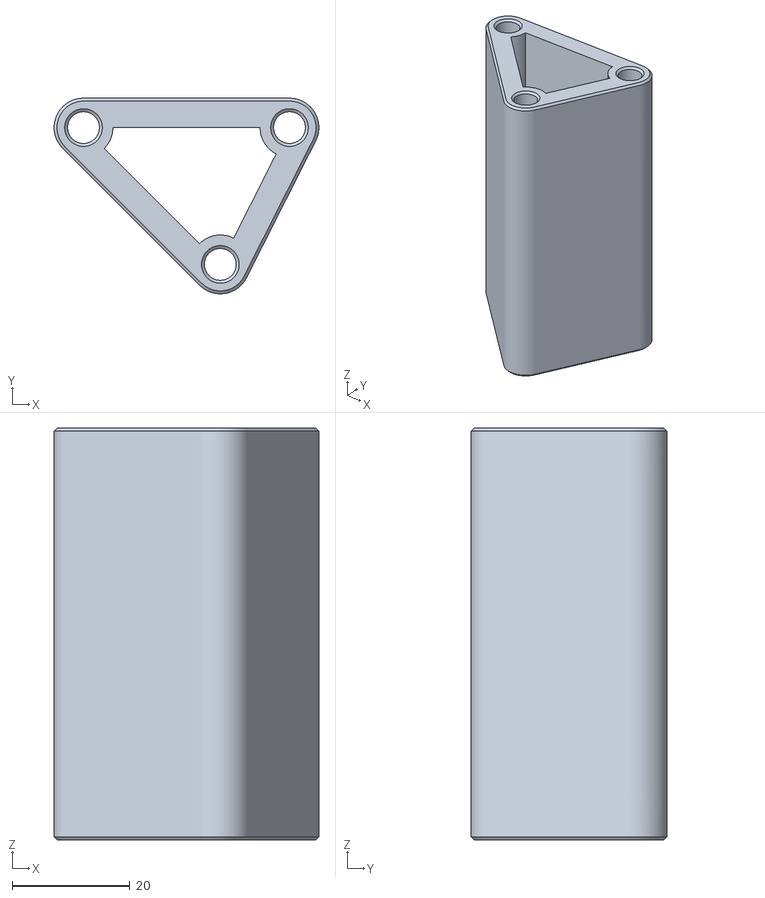
[picture p75: CAD file, 2021-02-19]
prusa mini/ejector 3.0/motor plate standoff.stl
45.0 x 33.2 x 70.0
