paenian/Delta-Conveyor-Belt/prusa mini/tensioner body(Mirror).stl

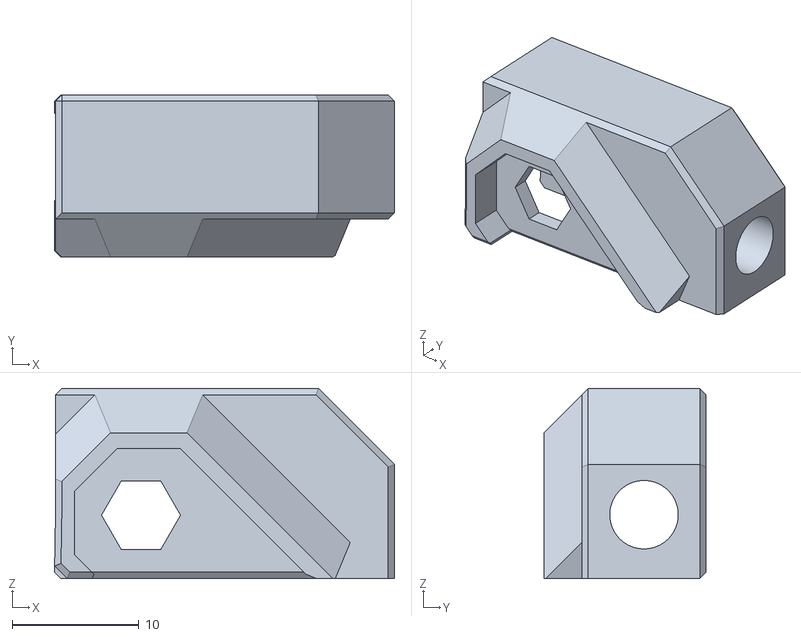
[picture p76: CAD file, 2020-10-02]
prusa mini/tensioner body(Mirror).stl
26.8 x 12.8 x 15.0
