paenian/Delta-Conveyor-Belt/kossel - 240mm triangle/extruder spacer.stl

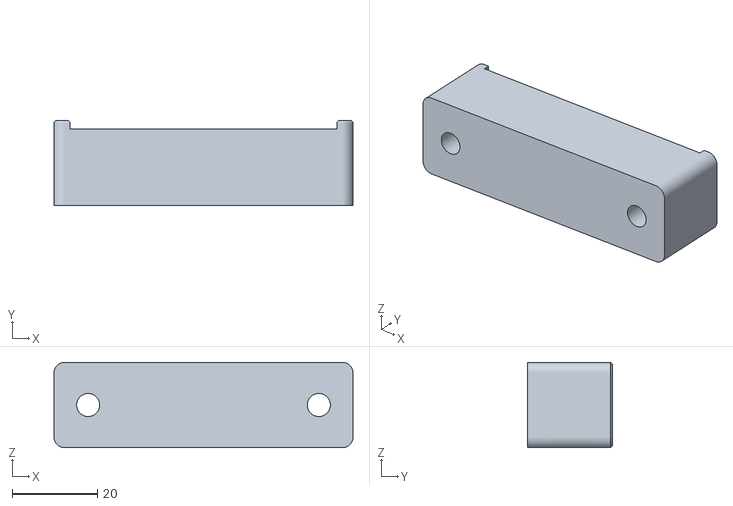
[picture p77: CAD file, 2020-04-07]
kossel - 240mm triangle/extruder spacer.stl
70.0 x 20.0 x 20.0
