paenian/Delta-Conveyor-Belt/prusa mini/tensioner rod holder.stl

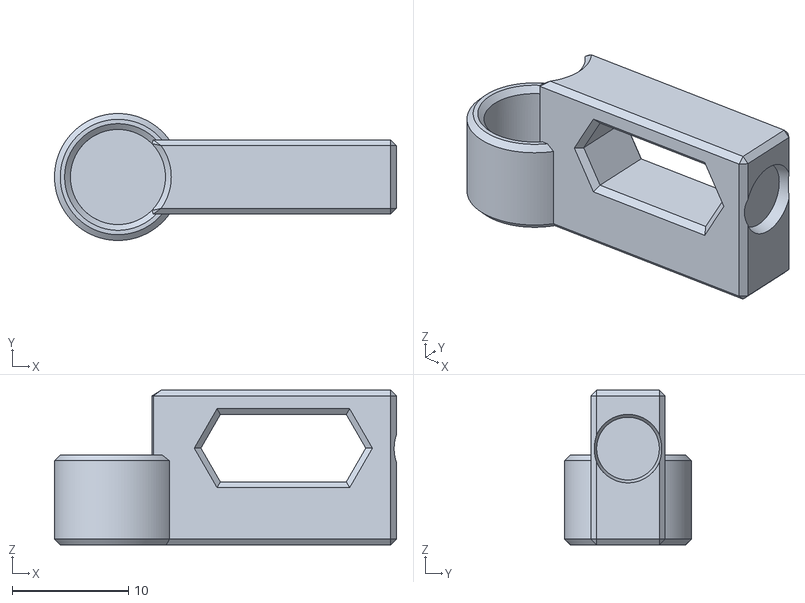
[picture p78: CAD file, 2020-10-02]
prusa mini/tensioner rod holder.stl
29.5 x 10.9 x 13.3
