paenian/Delta-Conveyor-Belt/tensioner arm.stl

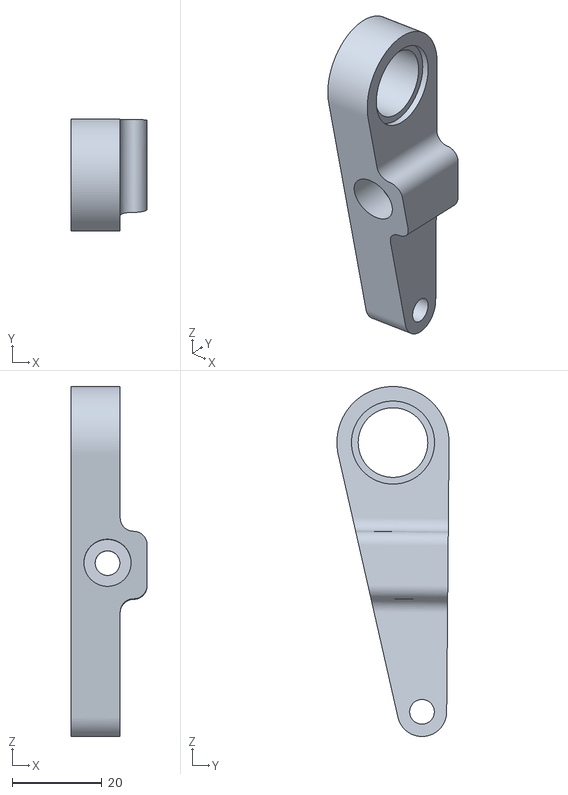
[picture p79: CAD file, 2020-03-01]
tensioner arm.stl
17.0 x 25.0 x 78.0
