paenian/Delta-Conveyor-Belt/kossel - 240mm triangle/tensioner body.stl

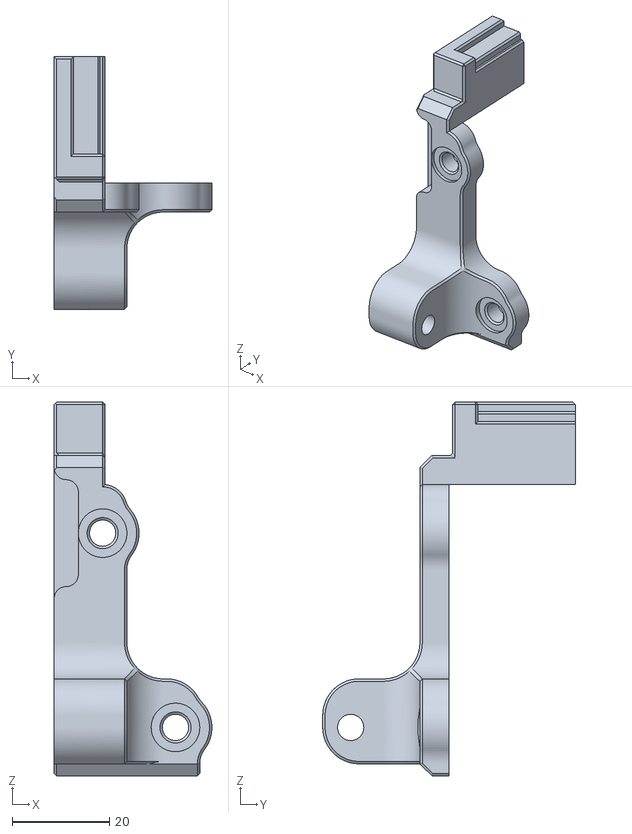
[picture p80: CAD file, 2020-04-07]
kossel - 240mm triangle/tensioner body.stl
32.5 x 52.0 x 77.0
