paenian/Delta-Conveyor-Belt/prusa mini/mini_belt_plate.stl

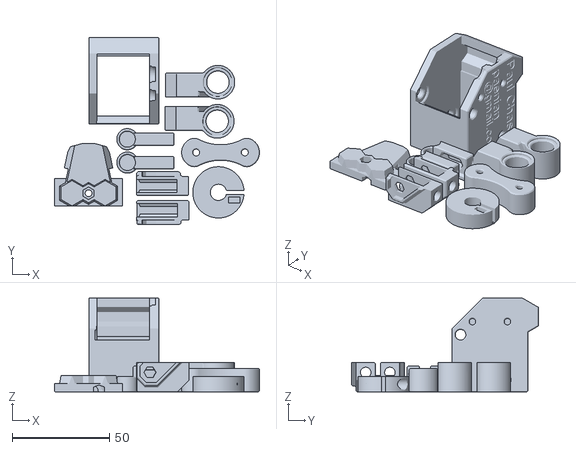
[picture p81: CAD file, 2020-10-02]
prusa mini/mini_belt_plate.stl
105.2 x 96.2 x 48.1
