paenian/Delta-Conveyor-Belt/tall tensioner base v1.stl

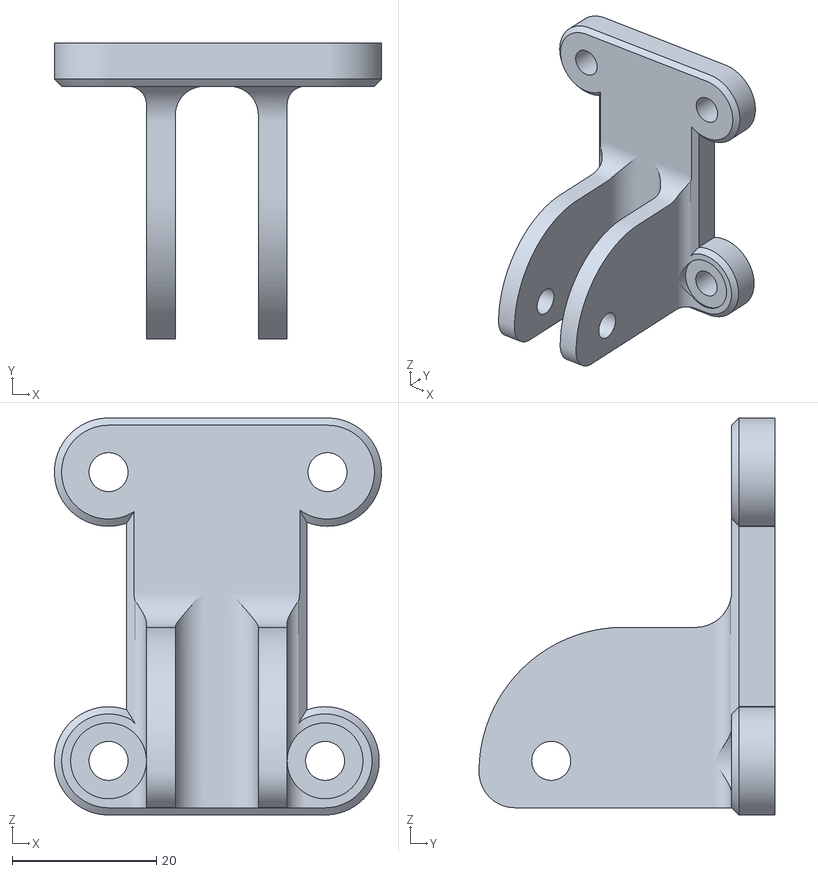
[picture p82: CAD file, 2020-03-01]
tall tensioner base v1.stl
45.3 x 41.0 x 55.0
