paenian/Delta-Conveyor-Belt/bertha drive bracket.stl

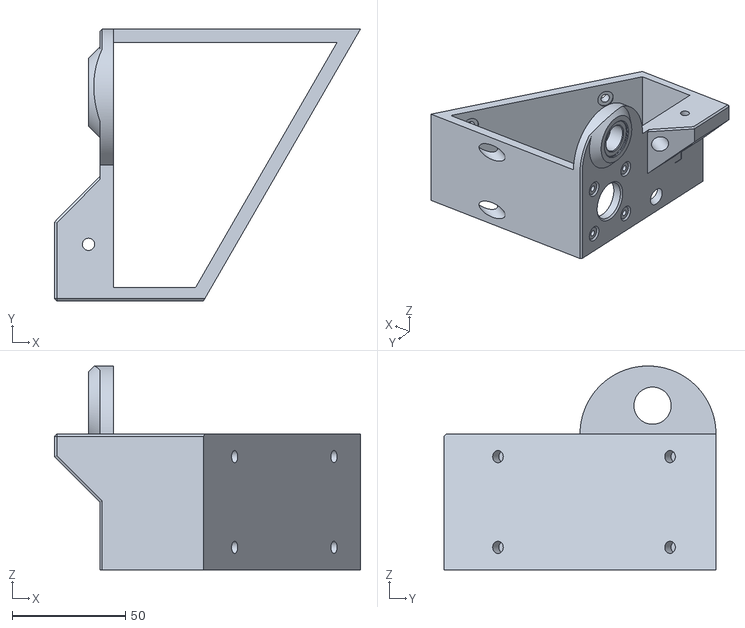
[picture p83: CAD file, 2020-03-01]
bertha drive bracket.stl
135.0 x 120.0 x 90.0
