paenian/Delta-Conveyor-Belt/prusa mini/MINI-heatbed-cable-cover-bottom.stl

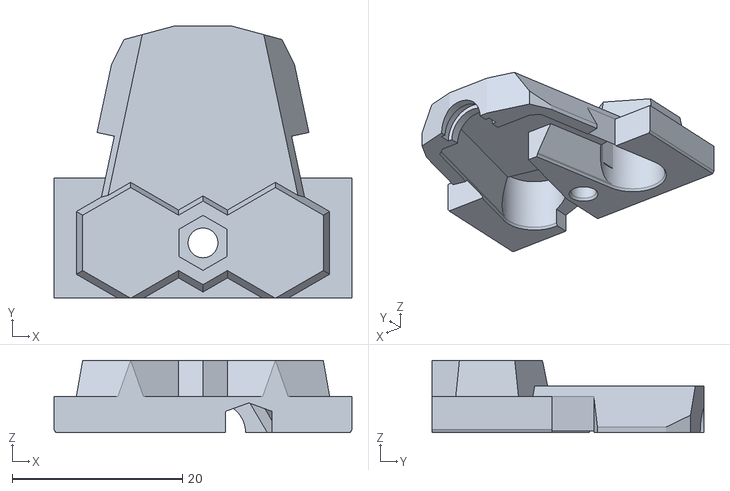
[picture p84: CAD file, 2020-10-02]
prusa mini/MINI-heatbed-cable-cover-bottom.stl
35.0 x 32.0 x 8.50
