paenian/Delta-Conveyor-Belt/prusa mini/belt motor mount.stl

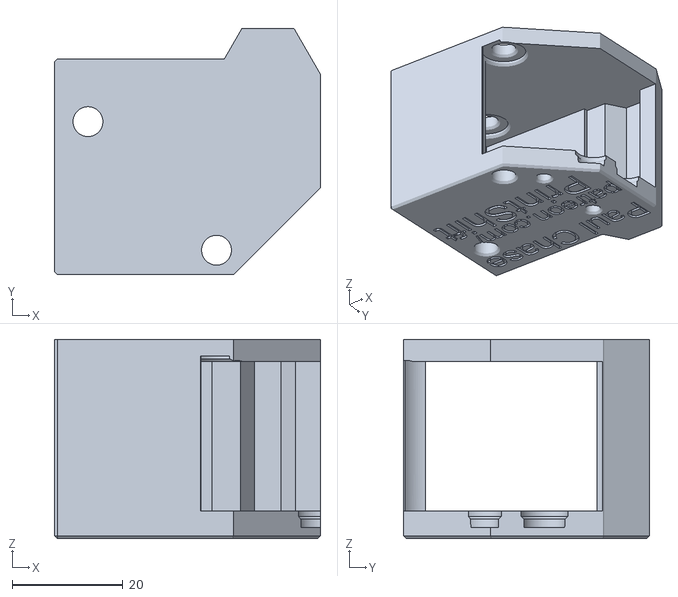
[picture p85: CAD file, 2020-10-02]
prusa mini/belt motor mount.stl
48.1 x 44.5 x 36.0
