paenian/Delta-Conveyor-Belt/bed bottom plate.dxf

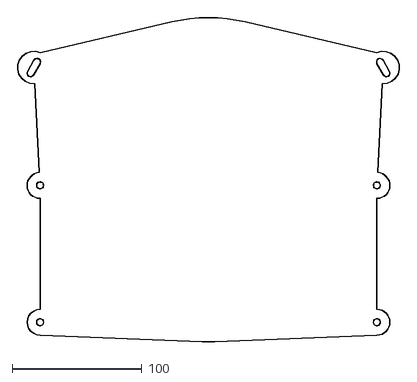
[picture p86: CAD file, 2019-11-17]
bed bottom plate.dxf
296.7 x 251.1
