paenian/Delta-Conveyor-Belt/kossel - 240mm triangle/foot.stl

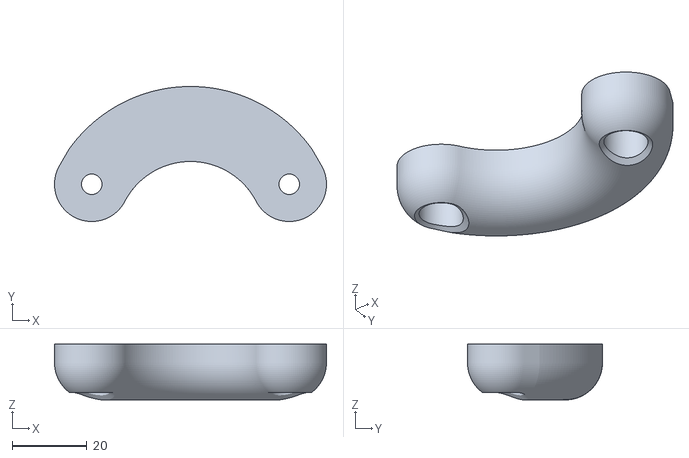
[picture p87: CAD file, 2020-04-07]
kossel - 240mm triangle/foot.stl
73.0 x 36.2 x 15.0
