paenian/Delta-Conveyor-Belt/bed plates + spacers.dxf

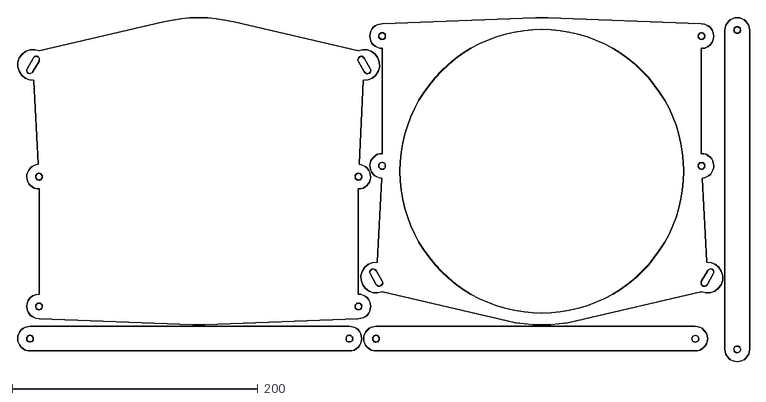
[picture p88: CAD file, 2019-11-17]
bed plates + spacers.dxf
596.8 x 281.1
