paenian/Delta-Conveyor-Belt/drive bracket.stl

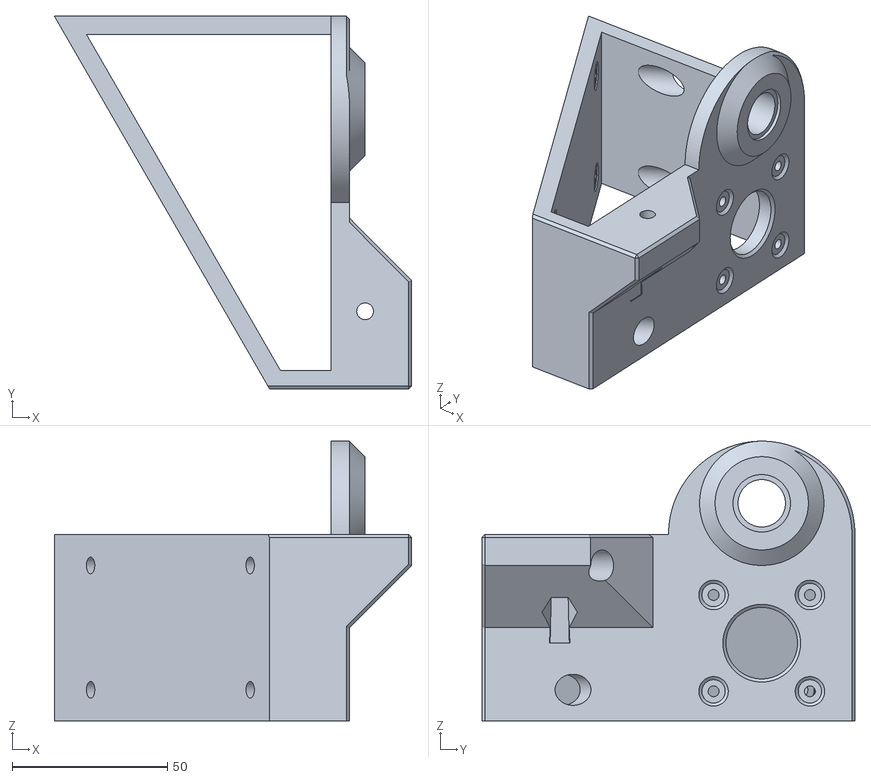
[picture p89: CAD file, 2019-11-17]
drive bracket.stl
115.0 x 120.0 x 90.0
