paenian/Delta-Conveyor-Belt/prusa mini/belt shaft mount - fixed bushing.stl

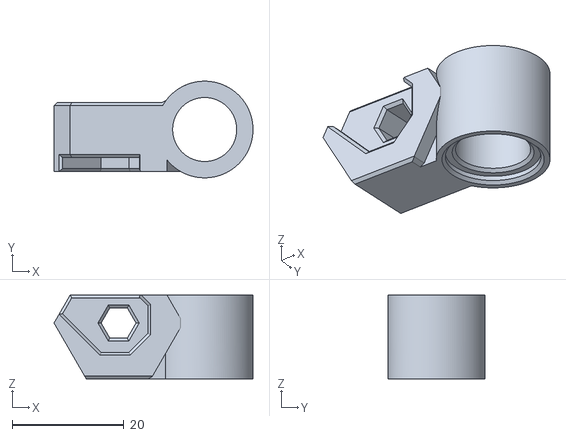
[picture p90: CAD file, 2020-08-09]
prusa mini/belt shaft mount - fixed bushing.stl
35.6 x 17.3 x 15.0
