paenian/Delta-Conveyor-Belt/drive_gear.stl

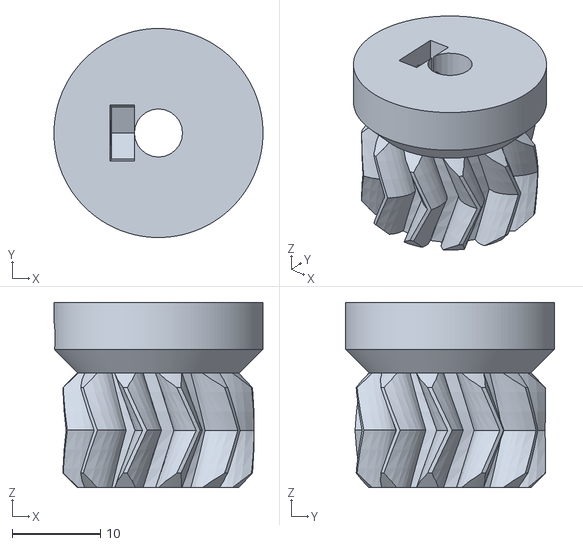
[picture p91: CAD file, 2019-11-17]
drive_gear.stl
23.7 x 23.7 x 21.0
