paenian/Delta-Conveyor-Belt/bed top plate.dxf

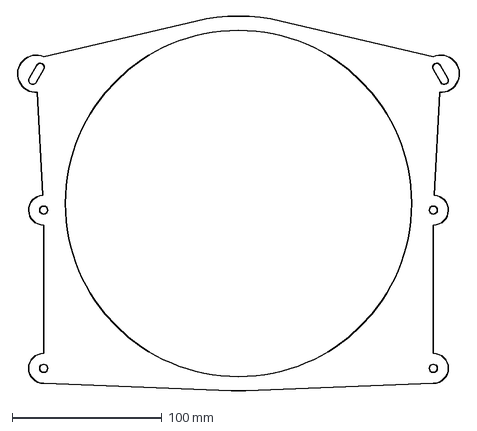
[picture p92: CAD file, 2019-11-17]
bed top plate.dxf
296.7 x 250.0 mm
