paenian/Delta-Conveyor-Belt/prusa mini/microswitch spacer.stl

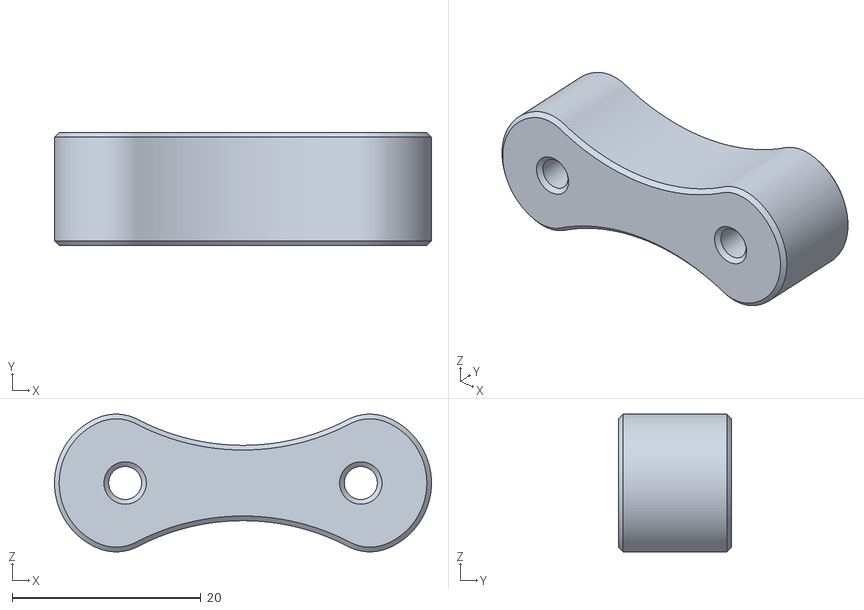
[picture p93: CAD file, 2020-08-09]
prusa mini/microswitch spacer.stl
40.0 x 12.0 x 14.6
