paenian/Delta-Conveyor-Belt/prusa mini/both_gears.stl

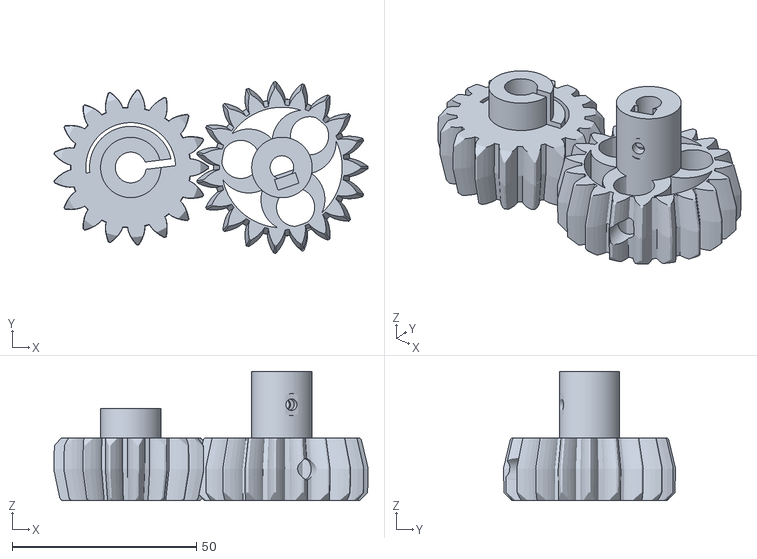
[picture p94: CAD file, 2020-08-09]
prusa mini/both_gears.stl
85.1 x 46.6 x 35.0
