paenian/Delta-Conveyor-Belt/tensioner base.stl

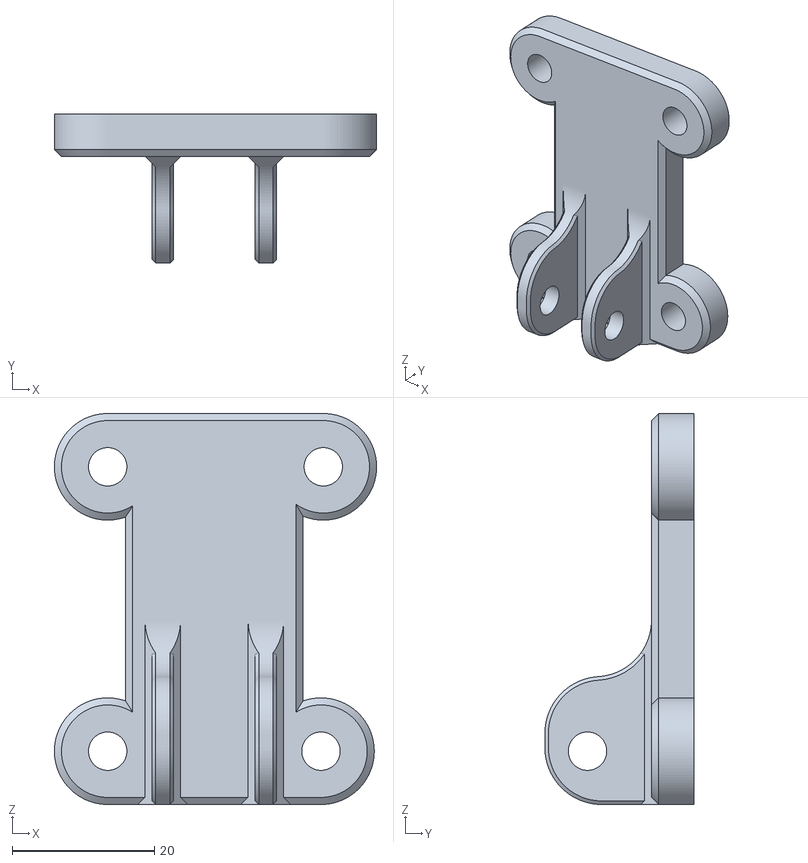
[picture p95: CAD file, 2019-11-17]
tensioner base.stl
45.3 x 21.0 x 55.0
