paenian/Delta-Conveyor-Belt/prusa mini/clamp.stl

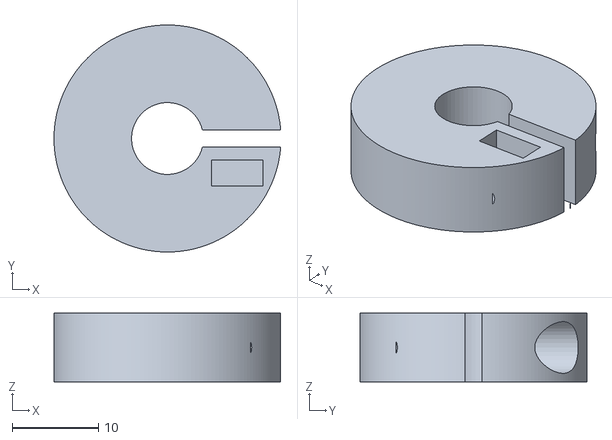
[picture p96: CAD file, 2020-08-09]
prusa mini/clamp.stl
26.3 x 26.3 x 8.00
