paenian/Delta-Conveyor-Belt/prusa mini/foot.stl

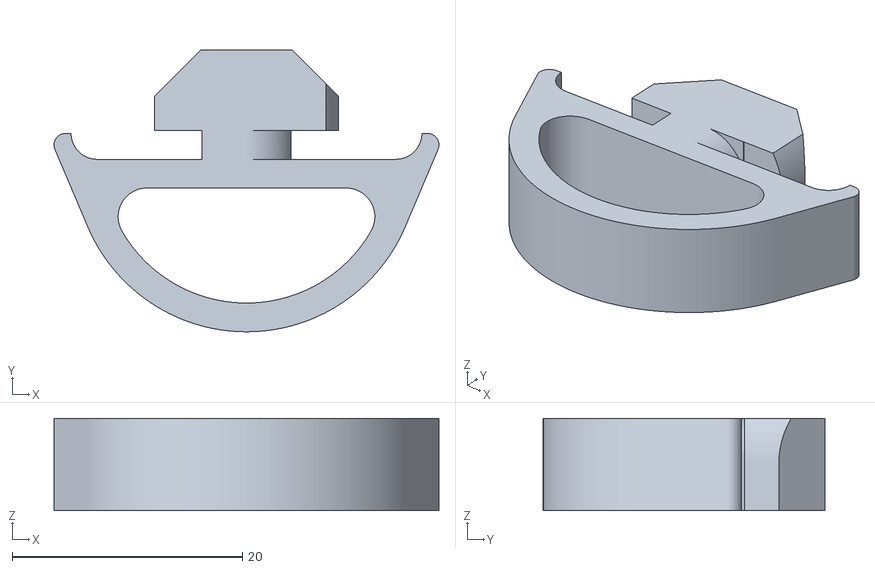
[picture p97: CAD file, 2020-08-09]
prusa mini/foot.stl
33.5 x 24.5 x 8.00
