paenian/Delta-Conveyor-Belt/prusa mini/3030 m3 tnut.stl

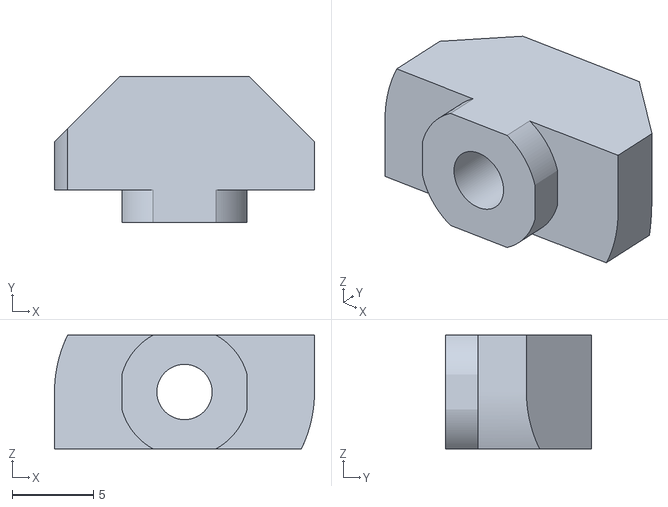
[picture p98: CAD file, 2020-08-09]
prusa mini/3030 m3 tnut.stl
16.0 x 8.99 x 7.00
